lucamar90/ritmo-code/firmware/ritmo_code/ritmo_code.ino

/**
 * Ritmo Code — monitor d'uso per Claude Code, schermo touch LVGL
 * Scheda: Guition JC4832W535 (ESP32-S3, AXS15231B QSPI), 480x320 orizzontale.
 *
 * Dashboard del rate-limit di Claude Code (finestre 5h e 7g, header unified-*),
 * sonda reale per modello (latenza + HTTP), proiezione di esaurimento della
 * finestra 5h e ritmo d'uso orario con filtro di periodo. Token OAuth inserito
 * sullo schermo e salvato cifrato (AES-256-GCM, chiave derivata da un PIN di 4 cifre).
 *
 * Nessun pulsante fisico: navigazione 100% touch (swipe tra le schermate + slideshow).
 * Init di display/touch validato nel bring-up (vedi RIFERIMENTO-HARDWARE-LVGL.md).
 */
#include <Arduino.h>
#include <Arduino_GFX_Library.h>
#include <lvgl.h>
#include <display/lv_display_private.h>   // perf_label / timer del contatore FPS
#include <Wire.h>
#include <WiFi.h>
#include <WebServer.h>
#include <Update.h>
#include <esp_ota_ops.h>
#include <ESPmDNS.h>
#include <Preferences.h>
#include <LittleFS.h>
#include <time.h>
#include <math.h>
#include "config.h"
#include "touch.h"
#include "wifi_manager.h"
#include "api.h"
#include "status.h"
#include "crypto.h"
#include "accounts.h"
#include "extras.h"         // meteo (Open-Meteo) e statistiche del PC per la home
#include "status_page.h"   // pagina di stato servita su /
#include "logo_assets.h"   // Clawd + logotipo ufficiali (generato da tools/gen_logo_assets.py)
struct NoticeText;                 // avviso a schermo intero (prototipi generati da Arduino)
struct AlertRec;                   // voce della cronologia degli avvisi (idem)
struct CdItem;                     // conto alla rovescia (idem)

// ---- Tema "Terminale": font JetBrains Mono (tools/gen_fonts.sh) ----
// 12/14 Regular, 22 Medium, 54 ExtraBold (solo cifre e %). I simboli che JetBrains
// Mono non ha (✻ ↻ ↵ ✎ e lo spinner di Claude Code) arrivano da DejaVu Sans Mono;
// i LV_SYMBOL_* della tastiera LVGL dal fallback Montserrat.
LV_FONT_DECLARE(font_jbm_12)
LV_FONT_DECLARE(font_jbm_14)
LV_FONT_DECLARE(font_jbm_22)
LV_FONT_DECLARE(font_jbm_54)
LV_FONT_DECLARE(font_jbm_96)
LV_FONT_DECLARE(font_jbm_150)
#define F12 (&font_jbm_12)
#define F14 (&font_jbm_14)
#define F22 (&font_jbm_22)
#define F54 (&font_jbm_54)
#define F96 (&font_jbm_96)                  // orologio: solo cifre, due punti e trattino
#define F150 (&font_jbm_150)                // orologio notturno a tutto schermo
#define U_SPARK   "\xE2\x9C\xBB"   // ✻
#define U_REFRESH "\xE2\x86\xBB"   // ↻
#define U_MENU    "\xE2\x89\xA1"   // ≡
#define U_LEFT    "\xE2\x86\x90"   // ←
#define U_RIGHT   "\xE2\x86\x92"   // →
#define U_ENTER   "\xE2\x86\xB5"   // ↵
#define U_UP      "\xE2\x86\x91"   // ↑
#define U_BKSP    "\xE2\x8C\xAB"   // ⌫
#define U_BLOCK   "\xE2\x96\x88"   // █
#define U_CURSOR  "\xE2\x96\x8C"   // ▌
#define U_MIDDOT  "\xC2\xB7"       // ·
#define U_PENCIL  "\xE2\x9C\x8E"   // ✎
#define U_CROSS   "\xE2\x9C\x95"   // ✕

// ---- Palette tema Terminale (stile Claude Code) ----
// Fondo terminale caldo, cornici a 1 px, un solo accento argilla; verde/ambra/rosso
// solo per lo stato.
#define C_BG       0x141413
#define C_SURFACE  0x1B1A18   // tasti e campi di testo
#define C_SURFACE2 0x23221F   // stato "premuto"
#define C_TRACK    0x2C2A27   // blocchi spenti
#define C_GRID     0x2C2A27   // griglie tratteggiate
#define C_BORDER   0x3A3834   // cornici
#define C_TEXT     0xE8E6DF
#define C_MUTED    0x8E8B82
#define C_FAINT    0x5C5A55
#define C_ACCENT   0xD97757   // argilla Claude
#define C_OK       0x9BC08A
#define C_WARN     0xE0B25A
#define C_BAD      0xE06C5A
#define C_BLUE     0x7DB9D6

// ---- Lingua (0 = italiano, 1 = english; Impostazioni -> NVS "lang") ----
// I font JetBrains Mono includono Latin-1: a schermo le lettere accentate ci sono.
static uint8_t g_lang = 0;
#define TRS(pt, en) (g_lang ? (en) : (pt))

// barra a blocchi: due label affiancate (piena + vuota) nello stesso font mono.
// Definita qui in cima: il preprocessore Arduino genera i prototipi prima del codice.
struct Blocks { lv_obj_t *on, *off; int n; };

// ---- Hardware ----
Arduino_Canvas *gfx = nullptr;
static uint16_t *canvas_fb = nullptr;
AXS15231B_Touch touch_dev(TOUCH_SCL, TOUCH_SDA, TOUCH_INT, TOUCH_ADDR, TOUCH_ROTATION);
WiFiManager g_wifi;
Preferences g_prefs;

// ---- Stato dell'applicazione ----
enum State {
  ST_BOOT, ST_PIN, ST_SETUP_PIN, ST_WIFI, ST_TOKEN,
  ST_LOADING, ST_MAIN, ST_SETTINGS, ST_ACCOUNTS, ST_ACCT_NAME, ST_ABOUT, ST_ERROR,
  ST_MODELS, ST_MODEL_EDIT, ST_OTA, ST_NETWORKS
};
static State g_state = ST_BOOT;
static State g_pending = ST_BOOT;
static bool  g_dirty = false;
static void request_state(State s) { g_pending = s; g_dirty = true; }

// ---- Dati ----
static UsageData   g_usage = {};
static ModelStatus g_status = {true, true, true, true, false};

// ---- Modelli sondati (1 per ciclo, a rotazione) ----
// Gli ID si cambiano dal browser (http://<ip>/models) o dal touch (Impostazioni ->
// Modelli) e restano in NVS ("mid0".."mid3"): quando Anthropic rinomina un modello
// basta aggiornare l'ID, senza riflashare. Il nome mostrato resta fisso perche' e'
// legato all'accessorio della mascotte. Nessuna richiesta in piu' alla API: la
// modifica azzera solo il risultato della sonda, che si rifa' al suo turno.
#define NMODELS 4
#define MODEL_ID_MAX 48
struct ModelInfo {
  const char *name; const char *defId; char id[MODEL_ID_MAX]; ProbeResult pr; uint32_t atMs;
  uint16_t lh[7]; uint8_t lhN;          // ultime latenze (mini-linea nella pagina Modelli)
};
static ModelInfo g_models[NMODELS] = {
  {"Haiku",  "claude-haiku-4-5-20251001", "", {0, 0}, 0},
  {"Sonnet", "claude-sonnet-5",           "", {0, 0}, 0},
  {"Opus",   "claude-opus-5-5",           "", {0, 0}, 0},
  {"Fable",  "claude-fable-5-1",          "", {0, 0}, 0},
};
static int g_probeIdx = 0;

// ---- Rete in background (task FreeRTOS sul core 0) ----
// Le chiamate HTTPS (utilizzo, status.claude.com, sonda modello) bloccavano il
// loop per 2-5 s: niente swipe ne' tocchi durante l'aggiornamento. Ora le esegue
// net_task sul core 0 (dove gira gia' lo stack WiFi), mentre LVGL resta libero sul
// core 1. Il task NON tocca mai LVGL, NVS o LittleFS: riempie g_net e alza
// g_netDone; il loop applica i risultati nel proprio thread (net_apply).
struct NetJob {
  // richiesta: scritta dal loop prima di svegliare il task
  char token[200];
  char modelId[MODEL_ID_MAX];
  int  modelIdx;
  uint32_t epoch;          // g_dataEpoch al momento della richiesta
  bool firstLoad;          // true = schermata di caricamento
  // risultato: scritto dal task
  UsageData usage;
  bool usageOk;
  ModelStatus status;
  bool statusOk;
  ProbeResult probe;
  bool probed;
  uint32_t durMs;
};
static NetJob g_net;
static TaskHandle_t g_netTask = nullptr;
static volatile bool g_netBusy = false;   // richiesta in corso (il task possiede g_net)
static volatile bool g_netDone = false;   // risultato pronto da applicare
static bool g_loadPending = false;        // ST_LOADING in attesa che il task sia libero
// Cambia quando token/account cambiano (switch, nuovo token, reset): un risultato
// partito prima appartiene ai dati vecchi e va scartato.
static uint32_t g_dataEpoch = 0;

// ID accettato: 3..47 caratteri a-z 0-9 . - _ (finisce dentro il JSON della sonda)
static bool model_id_valid(const char *v) {
  size_t n = strlen(v);
  if (n < 3 || n >= MODEL_ID_MAX) return false;
  for (size_t i = 0; i < n; i++) {
    char c = v[i];
    if (!((c >= 'a' && c <= 'z') || (c >= '0' && c <= '9') || c == '-' || c == '.' || c == '_'))
      return false;
  }
  return true;
}
static void model_key(int i, char *key, size_t sz) { snprintf(key, sz, "mid%d", i); }
static void models_load() {
  for (int i = 0; i < NMODELS; i++) {
    char key[8]; model_key(i, key, sizeof(key));
    String v = g_prefs.isKey(key) ? g_prefs.getString(key, "") : String();
    strlcpy(g_models[i].id, (v.length() && model_id_valid(v.c_str())) ? v.c_str() : g_models[i].defId,
            MODEL_ID_MAX);
  }
}
// Imposta l'ID del modello i. Vuoto = torna al predefinito. Toglie spazi e
// maiuscole (copia-incolla dalla documentazione). false = ID non valido.
static bool model_set_id(int i, const char *raw) {
  if (i < 0 || i >= NMODELS || !raw) return false;
  char v[MODEL_ID_MAX + 1];
  size_t n = 0;
  for (const char *c = raw; *c; c++) {
    if (*c == ' ' || *c == '\t' || *c == '\r' || *c == '\n') continue;
    if (n >= MODEL_ID_MAX) return false;               // troppo lungo
    v[n++] = (*c >= 'A' && *c <= 'Z') ? (char)(*c + 32) : *c;
  }
  v[n] = 0;
  char key[8]; model_key(i, key, sizeof(key));
  const char *next;
  if (!v[0] || !strcmp(v, g_models[i].defId)) {
    if (g_prefs.isKey(key)) g_prefs.remove(key);
    next = g_models[i].defId;
  } else {
    if (!model_id_valid(v)) return false;
    g_prefs.putString(key, v);
    next = v;
  }
  if (strcmp(next, g_models[i].id) != 0) {
    strlcpy(g_models[i].id, next, MODEL_ID_MAX);
    g_models[i].pr.code = 0; g_models[i].pr.ms = 0; g_models[i].pr.msg[0] = 0;   // "--" fino alla prossima sonda
    g_models[i].atMs = 0;
    g_models[i].lhN = 0;
    Serial.printf("[MODEL] %s -> %s\n", g_models[i].name, g_models[i].id);
  }
  return true;
}


// ---- Token / sicurezza ----
static AccountSlots g_accts;
static EncryptedBlob g_blob;
static bool g_hasToken = false;              // esiste un account salvato in NVS
static bool g_onboarding = false;            // primo setup in corso
static char g_token[200] = {0};              // token decifrato (solo in RAM)
static char g_pendingToken[200] = {0};       // token inserito, in attesa del PIN
// PIN di sessione: resta in RAM dallo sblocco fino al riavvio, perche' cambiare account
// e aggiungerne uno richiedono di decifrare/cifrare ALTRI slot senza richiedere il PIN.
// Compromesso accettato: non indebolisce il modello — il token vive GIA' decifrato in
// g_token, quindi chi riesce a leggere la RAM ha gia' cio' che conta. Resta valido
// che: niente di tutto questo finisce in NVS, e factory_reset() azzera questo buffer.
static char g_sessionPin[PIN_LEN + 1] = {0};
static int  g_tokenTargetSlot = 0;
static char g_pendingLabel[ACCT_LBL_MAX] = {0};
static char g_pinEntry[PIN_LEN + 1] = {0};   // cifre in digitazione
static bool g_pinForWipe = false;            // schermata PIN aperta per confermare "cancella tutto"
static char g_pinFirst[PIN_LEN + 1] = {0};   // 1° inserimento nel setup del PIN
static bool g_pinConfirming = false;         // setup: conferma (2° inserimento)
static int  g_pinAttempts = 0;               // tentativi errati (persistito)
static uint32_t g_lockoutUntil = 0;          // millis fino al prossimo tentativo consentito
static bool g_timeInit = false;

// ---- Refresh in background ----
static bool g_wantRefresh = false;        // il pulsante di refresh ha chiesto un aggiornamento
static bool g_refreshing = false;         // richiesta in corso
static bool g_lastFetchOk = true;         // l'ultimo fetch e' andato a buon fine?
static char g_lastErr[64] = "";           // errore dell'ultimo fetch fallito (pannello web, /api/status)
static uint32_t g_lastErrAt = 0;          // epoch dell'errore
static int g_failN = 0;                   // fetch falliti di fila
static uint32_t g_lastOkMs = 0;           // millis dell'ultimo successo (per "aggiornato Xs fa")
static lv_obj_t *g_hdrStatus = nullptr;   // testo di stato nell'intestazione del dashboard

// ---- Fuso orario ----
// TZ_ROME usa la regola POSIX CET/CEST: l'ora legale cambia da sola (ultima
// domenica di marzo / ottobre). Gli altri valori sono offset GMT fissi.
#define TZ_ROME     99
#define TZ_ROME_RULE "CET-1CEST,M3.5.0,M10.5.0/3"

// ---- Luminosita' ----
static const uint8_t BRI_LEVELS[3] = {60, 160, 255};
static int g_briIdx = 1;
// luminosita' automatica: piena di giorno, bassa la sera (NVS "autobri")
// 0 spento, 1 col sole (tramonto-alba dal meteo, altrimenti 20-07), 2 20:00-07:00, 3 21:00-07:00
static int g_autoBri = 0;
// promemoria pausa (NVS "brk"): dopo N minuti di PC in uso senza staccare (dal PC Monitor)
static int g_brkIdx = 0;
static const uint8_t BRK_MIN[4] = {0, 45, 60, 90};
// avviso settimana (NVS "wkal"): sopra la soglia, se a questo ritmo la quota finisce almeno
// 12 ore prima del reset. Una volta per settimana ("wkald" = reset della settimana avvisata)
static int g_wkAlIdx = 2;
static const uint8_t WK_AL_THR[4] = {0, 70, 85, 95};
static uint32_t g_wkAlDone = 0;
// tasti della tendina (NVS "shbtn"): un bit per tasto, al massimo quattro
enum { SHB_PAUSE = 0, SHB_TIMER, SHB_LIGHT, SHB_SOUND, SHB_REFRESH, SHB_CAL, SHB_WX, SHB_MEDIA, SHB_CD, SHB_N };
static uint16_t g_shBtn = 0x0F;
// Claude oggi (NVS "ccd" giorno, "ccn" richieste finite, "cct" secondi di lavoro, "ccx" la piu' lunga)
static long g_ccDay = 0;
static int  g_ccN = 0;
static uint32_t g_ccT = 0, g_ccX = 0;
// ---- Media in riproduzione sul PC (PC Monitor 1.8): pagina a tutto schermo con copertina 160x160 ----
#define MC_N 160
static bool g_mediaAuto = true;                  // la pagina si apre da sola quando parte la riproduzione (NVS "mauto")
static bool g_mediaFast = false;                 // pagina aperta: il PC si legge ogni secondo
static uint8_t *g_mcImg = nullptr, *g_mcTmp = nullptr;   // copertina (PSRAM): mostrata / in arrivo dal task extra
static lv_image_dsc_t g_mcDsc;
static bool g_mcHave = false;
static uint32_t g_mcId = 0, g_mcWant = 0, g_mcGot = 0, g_mcPosAtMs = 0;
static volatile bool g_mcReq = false, g_mcDone = false, g_mcOk = false, g_mcActReq = false;
static char g_mcHost[48], g_mcAct[10];
static volatile bool g_ssReq = false;           // pagina sessioni: apri la sessione g_ssKey sul PC
static char g_ssHost[48], g_ssKey[10];
static bool g_ssTab = true;                     // cerca anche la scheda giusta in Warp (NVS "sstab")
static char g_ssAskK[10] = "";                  // ultima sessione toccata (esito sotto il riquadro)
// sulla pagina sessioni gli avvisi di Claude non aprono lo schermo intero: lampeggia il riquadro
// della sessione che ha appena finito o che aspetta te (fino al tocco o per 60 s)
static char g_ssBlinkK[6][10];
static uint32_t g_ssBlinkMs[6];
static char g_ssPrevK[6][10];
static int g_ssPrevS[6];
static uint32_t g_ssAskMs = 0;
static int g_mcSec = 0;
// ---- Conto alla rovescia verso una data (NVS "cd0".."cd2": "epoch|titolo"), dal dispositivo o dal browser ----
struct CdItem { uint32_t at; char title[44]; };
#define CD_MAX 3
static CdItem g_cd[CD_MAX];
static int g_cdN = 0, g_cdSel = 0;
static bool g_cdAlerted[CD_MAX];
static void cd_load();
static void cd_view_refresh();                  // ridisegna la pagina se e' aperta
static int cd_home_idx(time_t now);             // il conto da mostrare in home, -1 nessuno
static void cd_view_build();
static void cd_parts(const CdItem &c, time_t now, char *big, char *unit, char *sub, size_t n);
static bool g_cdOpen = false;                   // conto alla rovescia o editor aperti

static uint32_t g_lastPollMs = 0;         // millis dell'ultimo poll (per la barra di refresh)
static int g_pollSec = DEFAULT_POLL_SEC;  // intervallo di aggiornamento (config, NVS)
static int g_tzOffset = TZ_ROME;          // fuso: TZ_ROME (ora legale auto) o offset GMT fisso, NVS
static int g_slideSec = 0;                // slideshow: 0=off, 5/10/15/30s (config, NVS)
static int g_heatSrc = 0;                 // pagina ritmo: 0 claude, 1 pomodoro (NVS "heats")
static int g_heatMode = 3;                // 0=oggi 1=7g 2=30g 3=tutto (config, NVS)
static bool g_resetAlert = true;          // avviso quando una finestra oltre l'80% si libera (NVS "rstal")
static bool g_pcSound = true;             // suoni e notifiche sul PC per gli avvisi (NVS "pcsnd")
static int  g_ccCloseIdx = 2;             // chiude da solo l'avviso di Claude: 5 s, 10 s, 30 s, mai (NVS "ccclose")
static const uint8_t CC_CLOSE_S[4] = {5, 10, 30, 0};
static int  g_ccAlert = 2;                // avvisi di Claude Code: 0 spento, 1 sempre, 2/3 fine lavoro oltre 1/5 min (NVS "ccal")

// ---- Diagnostica prestazioni (Impostazioni -> Contatore FPS, NVS "perf") ----
// A schermo: overlay LVGL "FPS, CPU / ms (render | flush)". Sul seriale ogni 2s:
// fps, tempo di rotazione del frame, tempo di invio QSPI, loop piu' lento e
// memoria libera. Il tempo delle chiamate di rete viene stampato a ogni refresh.
// Nota: con il render FULL anche l'overlay stesso forza un ridisegno ogni ~300ms.
static bool g_perfOn = false;
struct PerfStats {
  uint32_t frames;
  uint64_t rotUs, copyUs, waitUs, txUs;
  uint32_t rotMaxUs, copyMaxUs, waitMaxUs, txMaxUs;
  uint32_t txFrames;       // frame inviati dal task del display (core 0)
  uint32_t loopMaxMs;
};
static PerfStats g_perf = {};
static uint32_t g_lastTouchMs = 0;        // ultimo tocco (mette in pausa lo slideshow)
// Notte / attenuazione (NVS "night", "nightp", "dim"). Valgono solo sul dashboard.
static const uint8_t NIGHT_FROM[4] = {0, 22, 23, 0};     // indice 0 = spento
static int  g_nightIdx = 0;                    // 0 spento, 1 22-07, 2 23-07, 3 00-07
static bool g_nightPause = true;               // di notte niente richieste ad Anthropic
static int  g_dimIdx = 0;                      // 0 spento, poi DIM_MIN minuti senza tocchi
static const uint8_t DIM_MIN[4] = {0, 1, 5, 10};
#define NIGHT_WAKE_MS 30000UL                  // di notte un tocco accende per 30 s
#define DIM_LEVEL 12                           // duty del backlight attenuato
static bool g_userPause = false;               // richieste messe in pausa dal tasto in testata (NVS "pause")
static uint32_t g_pauseUntil = 0;              // epoch di ripresa automatica, 0 = senza limite (NVS "pauseu")
static int  g_clockIdx = 0;                    // torna alla home dopo: 0 spento, poi CLOCK_MIN minuti (NVS "clock")
static const uint8_t CLOCK_MIN[4] = {0, 2, 5, 10};
// ---- Home: meteo e PC (task "extra" sul core 0, mai richieste ad Anthropic) ----
static float g_wxLat = DEFAULT_WX_LAT, g_wxLon = DEFAULT_WX_LON;   // NVS "wxlat", "wxlon"
static char  g_wxCity[32] = DEFAULT_WX_CITY;                        // NVS "wxcity"
static char  g_pcHost[48] = DEFAULT_PC_HOST;                        // NVS "pchost" (Ritmo Code PC Monitor, ip:porta)
static float g_kwhPrice = 0.30f;                                    // euro per kWh (NVS "kwh", /home)
static WeatherData g_wx = {};
static PcStats g_pc = {};
static uint32_t g_wxAtMs = 0, g_wxTryMs = 0, g_pcAtMs = 0, g_pcTryMs = 0;
static volatile bool g_wxReq = false, g_wxDone = false, g_pcReq = false, g_pcDone = false;
static WeatherData g_wxRes = {};
static PcStats g_pcRes = {};
static char g_pcReqHost[48] = {0};
// avviso da mandare al PC (task "extra"): l'ultimo vince
struct PcNotify { char host[48], ev[8], title[64], msg[96]; };
static PcNotify g_pcNtf = {};
static volatile bool g_pcNtfReq = false;
static SemaphoreHandle_t g_httpsLock = nullptr;
#define PC_HIST 240                                 // grafici: un punto per lettura (1 s = 4 min, 5 s = 20 min)
static int g_pcIntIdx = 0;                          // intervallo di lettura del PC (NVS "pcint")
static const uint16_t PC_INT_S[4] = {1, 3, 5, 60};
static uint32_t g_pcHistAtMs = 0;
// il PC e' considerato spento se non risponde da 3 letture (almeno 20 s)
static uint32_t pc_stale_ms() { uint32_t m = 3000UL * PC_INT_S[g_pcIntIdx]; return m < 20000UL ? 20000UL : m; }
static uint32_t pc_int_ms() { return g_mediaFast ? 1000UL : PC_INT_S[g_pcIntIdx] * 1000UL; }
static void pc_poll_in(uint32_t ms) { g_pcTryMs = millis() + ms + 50 - pc_int_ms(); }   // prossima lettura tra ms
static uint8_t g_pcHist[3][PC_HIST];               // cpu, gpu, ram in %
static int g_pcHistN = 0;
static lv_point_precise_t g_pcSparkPts[3][PC_HIST];   // una sola connessione TLS alla volta (RAM interna)
static uint8_t g_screenMode = 0;               // 0 normale, 1 attenuato, 2 spento, 3 orologio notturno
static bool g_nightClock = true;               // di notte: orologio tenue invece dello schermo spento (NVS "nightclk")
static int  g_nightBri = 0;                    // luminosita' dell'orologio notturno: 0 tenue, 1 molto tenue (NVS "nightbri")
static const uint8_t NIGHT_BRI[2] = {18, 6};
static bool g_touchSwallow = false;            // il tocco che risveglia non preme nulla
static uint32_t g_lastSlideMs = 0;

// ---- Storico (ring buffer; persistito in LittleFS) ----
#define HIST_MAX 160
struct Sample { uint32_t t; uint8_t h5; uint8_t d7; };   // t = epoch (0 = orologio non sincronizzato)
static Sample g_hist[HIST_MAX];
static int g_histN = 0;
static int g_histHead = 0;
static float g_hourBurn[24] = {0};   // consumo per ora del giorno (da sempre)
static float g_lastH5 = -1.0f;       // ultimo utilizzo 5h (delta dell'heatmap)

// ---- Picco di ogni settimana (per account, /weeks<slot>.bin) ----
#define NWEEKS 12
struct WeekRec { uint32_t reset; uint8_t peak; };    // reset = epoch di fine settimana
static WeekRec g_weeks[NWEEKS];
static int g_weekN = 0;

// ---- Heatmap per giorno (per il filtro oggi/7g/30g) ----
#define NDAYS 31
struct DayHeat { uint32_t day; float burn[24]; };   // day = giorni locali dall'epoch
static DayHeat g_days[NDAYS];
static int g_dayN = 0;

// ---- Mascotte Clawd ufficiali (pagina modelli; umore in base allo stato) ----
// mood: 0=mai sondato, 1=ok, 2=limitato(429), 3=errore/incidente, 4=n/d(404)
struct Mascot { lv_obj_t *cont, *img, *lid[2], *drop; int baseY, mood; };
static Mascot g_masc[NMODELS];
static int g_mascN = 0;
static lv_point_precise_t g_mXPts[NMODELS][4][2];   // occhi a X (mood 3)

// ---- Puntatori UI del dashboard (azzerati a ogni build di ST_MAIN) ----
#define NTILES 8
// Pagine: l'ordine si sceglie in Impostazioni > schermo > ordine pagine (NVS "porder"); la home resta
// la prima. g_pageOrder[tile] = pagina mostrata in quella posizione.
enum { PG_HOME = 0, PG_ORA, PG_SESS, PG_MODELS, PG_5H, PG_RITMO, PG_WEEKS, PG_PC };
static uint8_t g_pageOrder[NTILES] = {PG_HOME, PG_ORA, PG_SESS, PG_MODELS, PG_5H, PG_RITMO, PG_WEEKS, PG_PC};
static int g_curTile = 0;
static int cur_page() { return g_pageOrder[g_curTile < NTILES ? g_curTile : 0]; }
static int tile_of(int pg) { for (int i = 0; i < NTILES; i++) if (g_pageOrder[i] == pg) return i; return 0; }
static const char *page_name(int pg);
#define NBLK 19                       // blocchi della barra di utilizzo
struct DashUI {
  lv_obj_t *tv, *tile[NTILES], *tab[NTILES];
  lv_obj_t *hdrPath, *hdrAcct, *refBar, *pauseBtn, *pauseBar[2], *pausePlay;
  lv_obj_t *hdrSpark, *hmClLegend;                // ✻ che gira e "claude · al lavoro" quando Claude lavora
  // ora
  lv_obj_t *agPct5, *agCd5, *agAt5, *agPct7, *agCd7, *agAt7;
  lv_obj_t *agFc5;                                // previsione della 5h sotto il conto alla rovescia
  lv_obj_t *ssBox[6], *ssLeg[6], *ssSt[6], *ssAge[6], *ssTi[6], *ssFt[6];   // pagina sessioni
  Blocks blk5, blk7;
  lv_obj_t *agWord, *agCursor, *agPace, *agPaceMark;
  // modelli
  lv_obj_t *mDot[NMODELS], *mName[NMODELS], *mSpark[NMODELS], *mLat[NMODELS], *mStat[NMODELS];
  lv_obj_t *mSum, *mInc;
  // finestra 5h
  lv_obj_t *trHist, *trProj, *trDot, *trCap, *trT0, *trT1;
  // ritmo
  lv_obj_t *heat[24], *heatBtn[4], *heatTab[2], *heatCap;
  // settimane
  lv_obj_t *wkBar[8], *wkVal[8], *wkDate[8], *wkCap;
  // home
  lv_obj_t *hmTime, *hmDate, *hmWxIcon, *hmTemp, *hmDesc, *hmRain, *hmSun;
  lv_obj_t *hmPct[2], *hmInfo[2], *hmRight[2];
  Blocks hmBlk[2];
  lv_obj_t *hmPcRow, *hmPcOff, *hmPcVal[4], *hmPcLegend;
  lv_obj_t *hmPauseRow;                           // "richieste" + "in pausa" (in giallo): due colori, due etichette
  lv_obj_t *hmCdLegend, *hmCdBig, *hmCdUnit, *hmCdSec;   // conto alla rovescia in home (a destra del riquadro claude)
  bool hmCdOn;
  // pc
  lv_obj_t *pcLeg[4], *pcMain[4], *pcSub[3], *pcSpark[3], *pcSys, *pcDisks;
  int hmWxCode;
};
static DashUI g_ui;
static lv_obj_t *g_pinDots = nullptr, *g_pinMsg = nullptr;

// punti delle linee del grafico di tendenza (devono restare validi)
static lv_point_precise_t g_trPts[HIST_MAX];
static lv_point_precise_t g_trProjPts[2];

// ---- Forward declarations ----
static void render_state();
static void refresh_ui_values();
static void dash_tick();
static void set_hdr_status();
static void apply_tz();
static void ui_pin();
static void ui_wifi();
static void ui_token();
static void ui_loading(const char *sub);
static void ui_main();
static void ui_settings();
static void ui_accounts();
static void ui_account_name();
static void ui_models();
static void perf_apply();
static void ui_model_edit();
static void ui_ota();
static void ui_networks();
static void ui_message(const char *title, const char *sub, uint32_t color);
static void nav_cb(lv_event_t *e);
static void start_data_web();
static void trend_redraw();
static void heat_redraw();
static void weeks_redraw();
static void home_redraw();
static void home_tick();
static void pc_redraw();
static void pause_menu_close();
static void show_moment(int win, int thr);
static void moment_tick();
static void moment_close();
static void cc_event(long id, const char *ev, const char *proj, int dur, int age);
static int g_setGroup = 0;
// calendario: link iCal (NVS "ical", segreto: lo legge solo il PC collegato) e prossimi eventi dal PC Monitor
static char g_ical[256] = "";
struct CalEv { uint32_t s, e; char title[64]; };
static CalEv g_cal[3];
static int g_calN = 0;
static int g_calAlIdx = 1;                   // avviso calendario: 0 spento, 1/2/3 = 5/10/15 min prima (NVS "calal")
static const uint8_t CAL_AL_MIN[4] = {0, 5, 10, 15};
static uint32_t g_calAlerted = 0;            // inizio dell'ultimo evento gia' avvisato
static CalEv g_calNotice;                    // evento dell'avviso a schermo
#define CAL_ALL_MAX 120
static CalItem *g_calTmp = nullptr;            // download del task extra, copiato nel loop
static int g_tmMenuMode = 0;                  // menu del timer: 0 tutto, 1 solo pomodoro, 2 solo timer
static bool g_ccFocusDefer = false;          // avvisi di Claude durante il focus: rimandati alla pausa (NVS "ccfocus")
static bool g_ccDeferred = false;            // un avviso di Claude aspetta la fine del focus
static bool tm_action(int opt);               // comandi del timer (menu del dispositivo e PC)
static uint32_t tm_left_s();
// pannello a tendina: il touch riconosce il gesto (giu' dalla testata / su per chiudere), il loop apre
static volatile int g_shadeReq = 0;               // 1 apri, 2 chiudi
static lv_obj_t *g_shade = nullptr;
// Aggiornamento del firmware dall'ultima release di GitHub: controllo (task extra) e installazione
// (task di rete: scrivere la flash da uno stack in PSRAM non si puo')
enum { UPD_IDLE = 0, UPD_CHECKING, UPD_AVAILABLE, UPD_UPTODATE, UPD_ERROR, UPD_INSTALLING, UPD_FAILED, UPD_REBOOT };
static volatile int g_updState = UPD_IDLE;
static volatile bool g_updCheckReq = false, g_updInstallReq = false, g_updRunning = false, g_updDone = false;
static volatile int g_updPct = 0;
static char g_updTag[16] = "", g_updUrl[200] = "";
static String g_updErr;
static uint32_t g_updCheckedMs = 0;
static uint32_t g_updCheckStartMs = 0;        // "controllo..." resta a schermo almeno 1,5 s
static void upd_progress(int pct) { g_updPct = pct; }
// "v3.9.3" piu' recente di FW_VERSION? (confronto numero per numero)
static bool ver_newer(const char *tag) {
  int a[3] = {0, 0, 0}, b[3] = {0, 0, 0};
  const char *t = tag; while (*t && !isdigit((unsigned char)*t)) t++;
  sscanf(t, "%d.%d.%d", &a[0], &a[1], &a[2]);
  sscanf(FW_VERSION, "%d.%d.%d", &b[0], &b[1], &b[2]);
  for (int i = 0; i < 3; i++) if (a[i] != b[i]) return a[i] > b[i];
  return false;
}                   // gruppo di impostazioni aperto (0 = pagina principale)
static char g_ccEv[8], g_ccProj[28];
static int  g_ccBusyN = 0;                      // sessioni di Claude Code al lavoro (PC Monitor)
static void cc_busy_ui();            // ultimo evento di Claude Code da mostrare
static void tm_menu_open(lv_event_t *e);
static void tm_label(char *out, size_t sz);
static uint32_t tm_color();
enum { TM_OFF = 0, TM_TIMER, TM_FOCUS, TM_BREAK };
static int  g_tmMode = TM_OFF;                // timer/pomodoro in corso
static int  g_pomoToday = 0;                  // pomodori completati oggi (NVS "pomn", giorno in "pomday")
static long g_pomoDay = 0;
static int  pomo_today();
static uint32_t g_tmEndMs = 0, g_tmLenS = 0;
static int  g_pomoN = 0;                      // pomodori completati nel ciclo in corso
// pomodoro: tre impostazioni pronte (focus / pausa / pausa lunga dopo il quarto, in minuti)
struct PomoPreset { uint8_t focus, brk, lng; };
static const PomoPreset POMO_PRESETS[3] = {{25, 5, 15}, {50, 10, 20}, {15, 3, 10}};
static int g_pomoPre = 0;                     // impostazione del ciclo in corso
#define POMO_FOCUS_S (POMO_PRESETS[g_pomoPre].focus * 60)
#define POMO_SHORT_S (POMO_PRESETS[g_pomoPre].brk * 60)
#define POMO_LONG_S  (POMO_PRESETS[g_pomoPre].lng * 60)
#define POMO_CYCLE   4

// ============================================================
// Pipeline di display/touch (validata nel bring-up)
// ============================================================
// Render PARZIALE: LVGL consegna solo le zone cambiate (a strisce, dal buffer
// piccolo in RAM interna). Ogni zona viene ruotata di 270 gradi nel framebuffer
// del Canvas (320x480, PSRAM) e, all'ultima zona del ciclo, il frame intero parte
// verso il pannello: l'AXS15231B di questa scheda non gestisce bene le finestre
// parziali, quindi l'invio resta a schermo intero.
// Mappatura invariata rispetto al bring-up: fb[(479 - x) * 320 + y] = pixel(x, y).
// Il ciclo esterno su x scrive il framebuffer in blocchi contigui (una riga del
// pannello per x): con la PSRAM dietro la cache e' ~decine di volte piu' veloce
// della vecchia copia a salti.
// ---- Invio del frame in parallelo (task "disp" sul core 0) ----
// L'invio QSPI del frame intero costa ~40 ms e prima bloccava LVGL. Ora:
//  - core 1 (LVGL) ruota le zone cambiate in canvas_fb, che resta l'immagine
//    completa e aggiornata;
//  - a fine frame aspetta che l'invio precedente sia finito, copia in tx_fb SOLO
//    il rettangolo cambiato in questo frame e sveglia il task;
//  - core 0 spedisce tx_fb al pannello mentre LVGL disegna gia' il frame dopo.
// tx_fb riceve ogni frame (nessuno viene saltato), quindi resta identico a
// canvas_fb dopo ogni copia: niente tearing, niente righe a meta' fra due frame.
static Arduino_GFX *g_panel = nullptr;        // driver AXS15231B (sotto al Canvas)
static uint16_t *tx_fb = nullptr;             // copia stabile del frame da inviare (PSRAM)
static SemaphoreHandle_t g_txIdle = nullptr;  // libero = nessun invio in corso
static TaskHandle_t g_txTask = nullptr;
static uint32_t g_frameRotUs = 0;
static int g_dirtyR0 = 480, g_dirtyR1 = -1, g_dirtyC0 = 320, g_dirtyC1 = -1;   // coordinate pannello

static void disp_tx_task(void *) {
  for (;;) {
    ulTaskNotifyTake(pdTRUE, portMAX_DELAY);
    uint32_t t0 = micros();
    g_panel->draw16bitRGBBitmap(0, 0, tx_fb, 320, 480);
    uint32_t tx = micros() - t0;
    g_perf.txFrames++;
    g_perf.txUs += tx; if (tx > g_perf.txMaxUs) g_perf.txMaxUs = tx;
    xSemaphoreGive(g_txIdle);
    // L'invio QSPI e' a polling e non cede mai la CPU: senza questa pausa, con lo
    // spinner che anima a ~27 fps e il TLS del task di rete sullo stesso core,
    // l'idle del core 0 non girava piu' e il task watchdog riavviava la scheda.
    vTaskDelay(1);
  }
}

static void disp_flush_cb(lv_display_t *disp, const lv_area_t *area, uint8_t *px_map) {
  uint32_t t0 = micros();
  const uint16_t *src = (const uint16_t *)px_map;
  int w = area->x2 - area->x1 + 1;
  int h = area->y2 - area->y1 + 1;
  for (int i = 0; i < w; i++) {
    uint16_t *dst = canvas_fb + (479 - (area->x1 + i)) * 320 + area->y1;
    const uint16_t *s = src + i;
    for (int j = 0; j < h; j++, s += w) dst[j] = *s;
  }
  // rettangolo cambiato, in coordinate del pannello (riga = 479 - x, colonna = y)
  if (479 - area->x2 < g_dirtyR0) g_dirtyR0 = 479 - area->x2;
  if (479 - area->x1 > g_dirtyR1) g_dirtyR1 = 479 - area->x1;
  if (area->y1 < g_dirtyC0) g_dirtyC0 = area->y1;
  if (area->y2 > g_dirtyC1) g_dirtyC1 = area->y2;
  g_frameRotUs += micros() - t0;

  if (lv_display_flush_is_last(disp)) {
    uint32_t t1 = micros();
    xSemaphoreTake(g_txIdle, portMAX_DELAY);          // invio precedente finito
    uint32_t t2 = micros();
    if (g_dirtyR1 >= g_dirtyR0 && g_dirtyC1 >= g_dirtyC0) {
      size_t n = (size_t)(g_dirtyC1 - g_dirtyC0 + 1) * sizeof(uint16_t);
      for (int r = g_dirtyR0; r <= g_dirtyR1; r++)
        memcpy(tx_fb + r * 320 + g_dirtyC0, canvas_fb + r * 320 + g_dirtyC0, n);
    }
    uint32_t t3 = micros();
    g_dirtyR0 = 480; g_dirtyR1 = -1; g_dirtyC0 = 320; g_dirtyC1 = -1;
    xTaskNotifyGive(g_txTask);                        // parte l'invio sul core 0

    uint32_t wait = t2 - t1, copy = t3 - t2;
    g_perf.frames++;
    g_perf.rotUs  += g_frameRotUs; if (g_frameRotUs > g_perf.rotMaxUs) g_perf.rotMaxUs = g_frameRotUs;
    g_perf.waitUs += wait;         if (wait > g_perf.waitMaxUs)        g_perf.waitMaxUs = wait;
    g_perf.copyUs += copy;         if (copy > g_perf.copyMaxUs)        g_perf.copyMaxUs = copy;
    g_frameRotUs = 0;
  }
  lv_disp_flush_ready(disp);
}
static void screen_apply();
static bool g_touchDown = false, g_gestDone = false;
static int16_t g_gestX = 0, g_gestY = 0;
static void touch_gesture_reset() { g_touchDown = false; }
static void touch_read_cb(lv_indev_t *indev, lv_indev_data_t *data) {
  uint16_t x, y;
  if (touch_dev.touched()) {
    touch_dev.readData(&x, &y);
    g_lastTouchMs = millis();          // mette in pausa lo slideshow durante l'interazione
    if (g_screenMode != 0) {           // schermo spento/attenuato: il tocco serve solo a risvegliare
      g_touchSwallow = true;
      g_screenMode = 0;
      screen_apply();
    }
    if (g_touchSwallow) { data->state = LV_INDEV_STATE_RELEASED; return; }
    // pannello a tendina: giu' partendo dalla testata apre, su chiude (piu' verticale che orizzontale)
    if (!g_touchDown) { g_touchDown = true; g_gestDone = false; g_gestX = x; g_gestY = y; }
    int16_t sx = g_gestX, sy = g_gestY; bool &done = g_gestDone;
    int dy = (int)y - sy, dx = abs((int)x - sx);
    if (!done && g_state == ST_MAIN) {
      if (!g_shade && sy < 40 && dy > 35 && dy > 2 * dx) { g_shadeReq = 1; done = true; }
      else if (g_shade && dy < -35 && -dy > 2 * dx)    { g_shadeReq = 2; done = true; }
      if (done) { g_touchSwallow = true; data->state = LV_INDEV_STATE_RELEASED; return; }
    }
    data->point.x = x; data->point.y = y;
    data->state = LV_INDEV_STATE_PRESSED;
  } else {
    g_touchSwallow = false;
    data->state = LV_INDEV_STATE_RELEASED;
    touch_gesture_reset();
  }
}

// ============================================================
// Helper di UI
// ============================================================
// Aggiornano una label solo se testo/colore cambiano davvero: ogni modifica
// invalida l'area e, con il pannello che vuole il frame intero, costa ~40 ms di invio.
static void label_set(lv_obj_t *l, const char *txt) {
  if (!l) return;
  const char *cur = lv_label_get_text(l);
  if (cur && strcmp(cur, txt) == 0) return;
  lv_label_set_text(l, txt);
}
static void label_color(lv_obj_t *l, uint32_t col) {
  if (!l) return;
  lv_color_t c = lv_color_hex(col);
  if (lv_color_eq(lv_obj_get_style_text_color(l, LV_PART_MAIN), c)) return;
  lv_obj_set_style_text_color(l, c, 0);
}
static lv_obj_t *mklabel(lv_obj_t *p, const char *txt, const lv_font_t *font, uint32_t color) {
  lv_obj_t *l = lv_label_create(p);
  lv_label_set_text(l, txt);
  lv_obj_set_style_text_font(l, font, 0);
  lv_obj_set_style_text_color(l, lv_color_hex(color), 0);
  return l;
}
static void no_box(lv_obj_t *o) {
  lv_obj_set_style_bg_opa(o, 0, 0);
  lv_obj_set_style_border_width(o, 0, 0);
  lv_obj_set_style_pad_all(o, 0, 0);
  lv_obj_clear_flag(o, LV_OBJ_FLAG_SCROLLABLE);
}
// colore per soglia, a gradini come in un terminale: <50 ok, <80 argilla, poi rosso
static uint32_t level_hex(float p) {
  if (p >= 80.0f) return C_BAD;
  if (p >= 50.0f) return C_ACCENT;
  return C_OK;
}
static lv_color_t grad_color(float p) { return lv_color_hex(level_hex(p)); }

// ---------- primitive del tema Terminale ----------
// Oggetti senza stili del tema LVGL: niente ombre, padding o sfondi da calcolare.
static lv_obj_t *plain_obj(lv_obj_t *p) {
  lv_obj_t *o = lv_obj_create(p);
  lv_obj_remove_style_all(o);
  lv_obj_clear_flag(o, LV_OBJ_FLAG_SCROLLABLE);
  lv_obj_clear_flag(o, LV_OBJ_FLAG_CLICKABLE);
  return o;
}
static lv_obj_t *hline(lv_obj_t *p, int x, int y, int w, uint32_t col) {
  lv_obj_t *o = plain_obj(p);
  lv_obj_set_pos(o, x, y); lv_obj_set_size(o, w, 1);
  lv_obj_set_style_bg_color(o, lv_color_hex(col), 0);
  lv_obj_set_style_bg_opa(o, LV_OPA_COVER, 0);
  return o;
}
// linea orizzontale tratteggiata: i punti devono restare validi (static)
static lv_point_precise_t PTS_W404[2] = {{0, 0}, {404, 0}};
static lv_point_precise_t PTS_W440[2] = {{0, 0}, {440, 0}};
static lv_obj_t *dline(lv_obj_t *p, int x, int y, lv_point_precise_t *pts) {
  lv_obj_t *l = lv_line_create(p);
  lv_obj_set_pos(l, x, y);
  lv_line_set_points(l, pts, 2);
  lv_obj_set_style_line_width(l, 1, 0);
  lv_obj_set_style_line_color(l, lv_color_hex(C_GRID), 0);
  lv_obj_set_style_line_dash_width(l, 3, 0);
  lv_obj_set_style_line_dash_gap(l, 3, 0);
  lv_obj_clear_flag(l, LV_OBJ_FLAG_CLICKABLE);
  return l;
}
// riquadro a filo sottile con il titolo inciso nella cornice
static lv_obj_t *tbox(lv_obj_t *p, int x, int y, int w, int h, const char *legend,
                      uint32_t col = C_BORDER, lv_obj_t **legendOut = nullptr) {
  lv_obj_t *b = plain_obj(p);
  lv_obj_set_pos(b, x, y); lv_obj_set_size(b, w, h);
  lv_obj_set_style_border_width(b, 1, 0);
  lv_obj_set_style_border_color(b, lv_color_hex(col), 0);
  lv_obj_set_style_radius(b, 4, 0);
  if (legend) {
    // Il titolo e' fratello del riquadro, non figlio: da figlio LVGL tagliava la parte
    // che sporge sopra il bordo. Sfondo pieno per "interrompere" la cornice.
    lv_obj_t *l = mklabel(p, legend, F12, C_MUTED);
    lv_obj_set_style_bg_color(l, lv_color_hex(C_BG), 0);
    lv_obj_set_style_bg_opa(l, LV_OPA_COVER, 0);
    lv_obj_set_style_pad_hor(l, 5, 0);
    lv_obj_set_pos(l, x + 8, y - 8);            // testo a x+13, allineato al rientro dei contenuti
    if (legendOut) *legendOut = l;
  }
  return b;
}
// pulsante: cornice 1 px, testo centrato, sfondo solo quando premuto
static lv_obj_t *tbtn(lv_obj_t *p, int x, int y, int w, int h, const char *txt, const lv_font_t *f,
                      uint32_t fg, uint32_t border, lv_event_cb_t cb, void *ud) {
  lv_obj_t *b = plain_obj(p);
  lv_obj_set_pos(b, x, y); lv_obj_set_size(b, w, h);
  lv_obj_set_style_border_width(b, 1, 0);
  lv_obj_set_style_border_color(b, lv_color_hex(border), 0);
  lv_obj_set_style_radius(b, 4, 0);
  lv_obj_set_style_bg_color(b, lv_color_hex(C_SURFACE2), LV_STATE_PRESSED);
  lv_obj_set_style_bg_opa(b, LV_OPA_COVER, LV_STATE_PRESSED);
  lv_obj_add_flag(b, LV_OBJ_FLAG_CLICKABLE);
  lv_obj_set_ext_click_area(b, 6);
  lv_obj_center(mklabel(b, txt, f, fg));
  if (cb) lv_obj_add_event_cb(b, cb, LV_EVENT_CLICKED, ud);
  return b;
}
// contenitore riga (flex) per comporre testi di colori diversi
static lv_obj_t *trow(lv_obj_t *p, int x, int y) {
  lv_obj_t *r = plain_obj(p);
  lv_obj_set_pos(r, x, y);
  lv_obj_set_size(r, LV_SIZE_CONTENT, LV_SIZE_CONTENT);
  lv_obj_set_flex_flow(r, LV_FLEX_FLOW_ROW);
  lv_obj_set_flex_align(r, LV_FLEX_ALIGN_START, LV_FLEX_ALIGN_END, LV_FLEX_ALIGN_END);
  return r;
}
static Blocks blocks_create(lv_obj_t *p, int x, int y, int n, const lv_font_t *f) {
  lv_obj_t *r = trow(p, x, y);
  Blocks b = { mklabel(r, "", f, C_ACCENT), mklabel(r, "", f, C_TRACK), n };
  return b;
}
static void blocks_set(Blocks &b, float pct, uint32_t col) {
  if (!b.on) return;
  int f = (int)(pct / 100.0f * b.n + 0.5f);
  if (pct > 0.5f && f == 0) f = 1;
  if (f < 0) f = 0; if (f > b.n) f = b.n;
  char on[3 * NBLK + 1] = "", off[3 * NBLK + 1] = "";
  for (int i = 0; i < f; i++) strcat(on, U_BLOCK);
  for (int i = f; i < b.n; i++) strcat(off, U_BLOCK);
  label_set(b.on, on);
  label_set(b.off, off);
  label_color(b.on, col);
}
// intestazione delle schermate secondarie: ✻ titolo, [← indietro], filo
static void nav_cb(lv_event_t *e);
static void thead(lv_obj_t *scr, const char *title, int backTo) {
  lv_obj_t *r = trow(scr, 13, 11);
  mklabel(r, U_SPARK " ", F14, C_ACCENT);
  mklabel(r, title, F14, C_TEXT);
  if (backTo >= 0)
    tbtn(scr, 378, 5, 89, 32, TRS(U_LEFT " indietro", U_LEFT " back"), F14, C_MUTED, C_BORDER, nav_cb, (void *)(intptr_t)backTo);
  hline(scr, 13, 42, 454, C_BORDER);
}
// riga chiave/valore toccabile (impostazioni, modelli, reti wifi)
static lv_obj_t *kv_row(lv_obj_t *list, const char *key, const char *val, uint32_t keyCol, uint32_t valCol,
                        lv_event_cb_t cb, void *ud, lv_obj_t **valOut = nullptr) {
  lv_obj_t *r = plain_obj(list);
  lv_obj_set_size(r, 454, 42);
  lv_obj_add_flag(r, LV_OBJ_FLAG_CLICKABLE);
  lv_obj_set_style_bg_color(r, lv_color_hex(C_SURFACE), LV_STATE_PRESSED);
  lv_obj_set_style_bg_opa(r, LV_OPA_COVER, LV_STATE_PRESSED);
  lv_obj_t *k = mklabel(r, key, F14, keyCol);
  lv_obj_align(k, LV_ALIGN_LEFT_MID, 13, 0);
  lv_obj_t *v = mklabel(r, val, F14, valCol);
  lv_obj_set_width(v, 230);
  lv_label_set_long_mode(v, LV_LABEL_LONG_DOT);
  lv_obj_set_style_text_align(v, LV_TEXT_ALIGN_RIGHT, 0);
  lv_obj_align(v, LV_ALIGN_RIGHT_MID, -13, 0);
  static lv_point_precise_t PTS_W454[2] = {{0, 0}, {454, 0}};
  dline(r, 0, 41, PTS_W454);
  if (cb) lv_obj_add_event_cb(r, cb, LV_EVENT_CLICKED, ud);
  if (valOut) *valOut = v;
  return r;
}
static lv_obj_t *tlist(lv_obj_t *scr, int x, int y, int w, int h) {
  lv_obj_t *l = plain_obj(scr);
  lv_obj_set_pos(l, x, y); lv_obj_set_size(l, w, h);
  lv_obj_set_flex_flow(l, LV_FLEX_FLOW_COLUMN);
  lv_obj_add_flag(l, LV_OBJ_FLAG_SCROLLABLE);
  lv_obj_set_scroll_dir(l, LV_DIR_VER);
  lv_obj_set_scrollbar_mode(l, LV_SCROLLBAR_MODE_AUTO);
  lv_obj_set_style_bg_color(l, lv_color_hex(C_FAINT), LV_PART_SCROLLBAR);
  lv_obj_set_style_bg_opa(l, LV_OPA_COVER, LV_PART_SCROLLBAR);
  lv_obj_set_style_width(l, 3, LV_PART_SCROLLBAR);
  return l;
}
// campo di testo e tastiera scuri (prima: tema chiaro di default di LVGL)
static void style_ta(lv_obj_t *ta) {
  lv_obj_set_style_bg_color(ta, lv_color_hex(C_SURFACE), 0);
  lv_obj_set_style_text_color(ta, lv_color_hex(C_TEXT), 0);
  lv_obj_set_style_text_font(ta, F14, 0);
  lv_obj_set_style_border_width(ta, 1, 0);
  lv_obj_set_style_border_color(ta, lv_color_hex(C_BORDER), 0);
  lv_obj_set_style_border_color(ta, lv_color_hex(C_ACCENT), LV_STATE_FOCUSED);
  lv_obj_set_style_radius(ta, 4, 0);
  lv_obj_set_style_pad_hor(ta, 12, 0);
  lv_obj_set_style_text_color(ta, lv_color_hex(C_FAINT), LV_PART_TEXTAREA_PLACEHOLDER);
  lv_obj_set_style_border_color(ta, lv_color_hex(C_ACCENT), LV_PART_CURSOR | LV_STATE_FOCUSED);
  lv_obj_set_style_shadow_width(ta, 0, 0);
}
static void style_kb(lv_obj_t *kb) {
  lv_obj_set_style_bg_color(kb, lv_color_hex(C_BG), 0);
  lv_obj_set_style_border_width(kb, 1, 0);
  lv_obj_set_style_border_side(kb, LV_BORDER_SIDE_TOP, 0);
  lv_obj_set_style_border_color(kb, lv_color_hex(C_BORDER), 0);
  lv_obj_set_style_pad_all(kb, 6, 0);
  lv_obj_set_style_pad_gap(kb, 4, 0);
  lv_obj_set_style_radius(kb, 0, 0);
  lv_obj_set_style_bg_color(kb, lv_color_hex(C_SURFACE), LV_PART_ITEMS);
  lv_obj_set_style_text_color(kb, lv_color_hex(C_TEXT), LV_PART_ITEMS);
  lv_obj_set_style_text_font(kb, F14, LV_PART_ITEMS);
  lv_obj_set_style_border_width(kb, 1, LV_PART_ITEMS);
  lv_obj_set_style_border_color(kb, lv_color_hex(C_TRACK), LV_PART_ITEMS);
  lv_obj_set_style_radius(kb, 3, LV_PART_ITEMS);
  lv_obj_set_style_shadow_width(kb, 0, LV_PART_ITEMS);
  lv_obj_set_style_bg_color(kb, lv_color_hex(C_SURFACE2), LV_PART_ITEMS | LV_STATE_PRESSED);
  lv_obj_set_style_bg_color(kb, lv_color_hex(C_BG), LV_PART_ITEMS | LV_STATE_CHECKED);
  lv_obj_set_style_text_color(kb, lv_color_hex(C_MUTED), LV_PART_ITEMS | LV_STATE_CHECKED);
  lv_obj_set_style_border_color(kb, lv_color_hex(C_BORDER), LV_PART_ITEMS | LV_STATE_CHECKED);
}
// spinner di Claude Code (· ✢ ✳ ✶ ✻ ✽ avanti e indietro): una label, 1 carattere
static const char *SPIN[10] = {"\xC2\xB7", "\xE2\x9C\xA2", "\xE2\x9C\xB3", "\xE2\x9C\xB6", "\xE2\x9C\xBB",
                               "\xE2\x9C\xBD", "\xE2\x9C\xBB", "\xE2\x9C\xB6", "\xE2\x9C\xB3", "\xE2\x9C\xA2"};
static lv_obj_t *g_spin = nullptr;
static void spin_tick() {
  static uint32_t last = 0; static int k = 0;
  if (!g_spin) return;
  uint32_t now = millis();
  if (now - last < 120) return;
  last = now; k = (k + 1) % 10;
  lv_label_set_text(g_spin, SPIN[k]);
}
// riga "✻ testo" centrata con lo spinner che gira
static lv_obj_t *spin_row(lv_obj_t *scr, const char *txt, int yOfs) {
  lv_obj_t *r = plain_obj(scr);
  lv_obj_set_size(r, LV_SIZE_CONTENT, LV_SIZE_CONTENT);
  lv_obj_set_flex_flow(r, LV_FLEX_FLOW_ROW);
  lv_obj_set_flex_align(r, LV_FLEX_ALIGN_START, LV_FLEX_ALIGN_CENTER, LV_FLEX_ALIGN_CENTER);
  lv_obj_set_style_pad_column(r, 8, 0);
  g_spin = mklabel(r, SPIN[0], F14, C_ACCENT);
  lv_obj_t *t = mklabel(r, txt, F14, C_TEXT);
  lv_obj_align(r, LV_ALIGN_CENTER, 0, yOfs);
  return t;
}
// "reset tra 1h 23m" / "2d 4h" / "ora" / "--" (orologio non sincronizzato)
static void fmt_eta(uint32_t epoch, char *out, int sz) {
  time_t now = time(nullptr);
  if (now < 1000000000L || epoch == 0) { snprintf(out, sz, "--"); return; }
  long d = (long)epoch - (long)now;
  if (d <= 0) { snprintf(out, sz, "%s", TRS("ora", "now")); return; }
  int days = d / 86400; d %= 86400;
  int hrs  = d / 3600;  d %= 3600;
  int mins = d / 60;
  if (days > 0)      snprintf(out, sz, "%dd %dh", days, hrs);
  else if (hrs > 0)  snprintf(out, sz, "%dh %02dm", hrs, mins);
  else               snprintf(out, sz, "%dm", mins);
}
static void fmt_clock(uint32_t epoch, char *out, int sz) {
  if (epoch == 0 || time(nullptr) < 1000000000L) { strlcpy(out, "--:--", sz); return; }
  time_t t = (time_t)epoch; struct tm tmv;
  localtime_r(&t, &tmv);
  if (!g_lang) {                         // %a e' sempre in inglese (locale C)
    static const char *GG[7] = {"Dom", "Lun", "Mar", "Mer", "Gio", "Ven", "Sab"};
    snprintf(out, sz, "%s %02d:%02d", GG[tmv.tm_wday % 7], tmv.tm_hour, tmv.tm_min);
    return;
  }
  strftime(out, sz, "%a %H:%M", &tmv);
}
static void fmt_hm(uint32_t epoch, char *out, int sz) {
  if (epoch == 0 || time(nullptr) < 1000000000L) { strlcpy(out, "--:--", sz); return; }
  time_t t = (time_t)epoch; struct tm tmv;
  localtime_r(&t, &tmv);
  strftime(out, sz, "%H:%M", &tmv);
}
// 1234 -> "1.2k", 2345678 -> "2.3M"

// ============================================================
// NVS / persistenza
// ============================================================
static void load_persisted() {
  g_prefs.begin(NVS_NAMESPACE, false);
  accountsLoad(g_prefs, g_accts);
  if (g_accts.used[g_accts.active] &&
      accountLoadBlob(g_prefs, g_accts.active, g_blob)) {
    g_hasToken = true;
  }
  g_pinAttempts = g_prefs.getInt("pinatt", 0);
  g_briIdx = g_prefs.getInt("bri", 1);
  g_autoBri = g_prefs.getInt("autobri", 0);
  if (g_autoBri < 0 || g_autoBri > 3) g_autoBri = 0;
  g_ssTab = g_prefs.getBool("sstab", true);
  {                                                  // ordine delle pagine: valido solo se e' una permutazione con la home prima
    uint8_t o[NTILES];
    if (g_prefs.getBytes("porder", o, NTILES) == NTILES && o[0] == PG_HOME) {
      uint8_t seen = 0; bool ok = true;
      for (int i = 0; i < NTILES; i++) { if (o[i] >= NTILES || (seen >> o[i]) & 1) ok = false; else seen |= 1 << o[i]; }
      if (ok) memcpy(g_pageOrder, o, NTILES);
    }
  }
  g_brkIdx = g_prefs.getInt("brk", 0);
  if (g_brkIdx < 0 || g_brkIdx > 3) g_brkIdx = 0;
  g_wkAlIdx = g_prefs.getInt("wkal", 2);
  if (g_wkAlIdx < 0 || g_wkAlIdx > 3) g_wkAlIdx = 2;
  g_wkAlDone = g_prefs.getUInt("wkald", 0);
  g_shBtn = (uint16_t)g_prefs.getUInt("shbtn", 0x0F);
  if (!g_shBtn || g_shBtn >= (1 << SHB_N)) g_shBtn = 0x0F;
  g_ccDay = g_prefs.getLong("ccd", 0);
  g_ccN = g_prefs.getInt("ccn", 0);
  g_ccT = g_prefs.getUInt("cct", 0);
  g_ccX = g_prefs.getUInt("ccx", 0);
  g_mediaAuto = g_prefs.getBool("mauto", true);
  cd_load();
  if (g_briIdx < 0 || g_briIdx > 2) g_briIdx = 1;
  g_pollSec = g_prefs.getInt("poll", DEFAULT_POLL_SEC);
  if (g_pollSec < MIN_POLL_SEC || g_pollSec > MAX_POLL_SEC) g_pollSec = DEFAULT_POLL_SEC;
  g_tzOffset = g_prefs.getInt("tz", TZ_ROME);
  if (g_tzOffset != TZ_ROME && (g_tzOffset < -12 || g_tzOffset > 14)) g_tzOffset = TZ_ROME;
  g_slideSec = g_prefs.getInt("slide", 0);
  if (g_slideSec != 0 && g_slideSec != 5 && g_slideSec != 10 &&
      g_slideSec != 15 && g_slideSec != 30) g_slideSec = 0;
  g_heatMode = g_prefs.getInt("heatm", 3);
  g_heatSrc = g_prefs.getInt("heats", 0) ? 1 : 0;
  g_perfOn = g_prefs.getBool("perf", false);
  g_resetAlert = g_prefs.getBool("rstal", true);
  g_pomoToday = g_prefs.getInt("pomn", 0);
  g_pomoDay = g_prefs.getLong("pomday", 0);
  g_pcSound = g_prefs.getBool("pcsnd", true);
  g_ccFocusDefer = g_prefs.getBool("ccfocus", false);
  strlcpy(g_ical, g_prefs.getString("ical", "").c_str(), sizeof(g_ical));
  g_calAlIdx = g_prefs.getInt("calal", 1);
  if (g_calAlIdx < 0 || g_calAlIdx > 3) g_calAlIdx = 1;
  g_ccCloseIdx = g_prefs.getInt("ccclose", 2);
  if (g_ccCloseIdx < 0 || g_ccCloseIdx > 3) g_ccCloseIdx = 2;
  g_ccAlert = g_prefs.getInt("ccal", 2);
  if (g_ccAlert < 0 || g_ccAlert > 3) g_ccAlert = 2;
  g_nightIdx = g_prefs.getInt("night", 0);
  if (g_nightIdx < 0 || g_nightIdx > 3) g_nightIdx = 0;
  g_nightPause = g_prefs.getBool("nightp", true);
  g_nightClock = g_prefs.getBool("nightclk", true);
  g_nightBri = g_prefs.getInt("nightbri", 0) ? 1 : 0;
  g_userPause = g_prefs.getBool("pause", false);
  g_pauseUntil = g_prefs.getUInt("pauseu", 0);
  g_clockIdx = g_prefs.getInt("clock", 0);
  g_pcIntIdx = g_prefs.getInt("pcint", 0);
  g_kwhPrice = g_prefs.getFloat("kwh", 0.30f);
  if (g_pcIntIdx < 0 || g_pcIntIdx > 3) g_pcIntIdx = 0;
  g_wxLat = g_prefs.getFloat("wxlat", DEFAULT_WX_LAT);
  g_wxLon = g_prefs.getFloat("wxlon", DEFAULT_WX_LON);
  strlcpy(g_wxCity, g_prefs.getString("wxcity", DEFAULT_WX_CITY).c_str(), sizeof(g_wxCity));
  strlcpy(g_pcHost, g_prefs.getString("pchost", DEFAULT_PC_HOST).c_str(), sizeof(g_pcHost));
  if (g_clockIdx < 0 || g_clockIdx > 3) g_clockIdx = 0;
  g_dimIdx = g_prefs.getInt("dim", 0);
  if (g_dimIdx < 0 || g_dimIdx > 3) g_dimIdx = 0;
  if (g_heatMode < 0 || g_heatMode > 3) g_heatMode = 3;
  g_lang = g_prefs.getInt("lang", 0) ? 1 : 0;
  models_load();
}
static void save_attempts() { g_prefs.putInt("pinatt", g_pinAttempts); }
static void apply_brightness() { if (g_screenMode == 0) ledcWrite(TFT_BL, BRI_LEVELS[g_briIdx]); }
static void screen_apply() {
  ledcWrite(TFT_BL, g_screenMode == 2 ? 0 : g_screenMode == 3 ? NIGHT_BRI[g_nightBri]
                    : (g_screenMode == 1 ? DIM_LEVEL : BRI_LEVELS[g_briIdx]));
}
// luminosita' automatica: al cambio giorno/sera imposta alta o bassa. Un tocco manuale vale
// fino al passaggio successivo; il livello scelto a mano in NVS non viene toccato.
static int hm_min(const char *hm, int dflt) {
  int h, m;
  if (!hm || sscanf(hm, "%d:%d", &h, &m) != 2 || h < 0 || h > 23 || m < 0 || m > 59) return dflt;
  return h * 60 + m;
}
static int g_autoBriPhase = -1;                      // -1 da ricalcolare, 0 giorno, 1 sera
static void auto_bri_tick(bool force) {
  static uint32_t last = 0;
  if (!force && millis() - last < 30000) return;
  last = millis();
  if (!g_autoBri) { g_autoBriPhase = -1; return; }
  time_t now = time(nullptr);
  if (now < 1000000000L) return;
  struct tm tv; localtime_r(&now, &tv);
  int cur = tv.tm_hour * 60 + tv.tm_min;
  int from = 20 * 60, to = 7 * 60;
  if (g_autoBri == 1 && g_wx.ok) { from = hm_min(g_wx.sunset, from); to = hm_min(g_wx.sunrise, to); }
  else if (g_autoBri == 3) from = 21 * 60;
  int phase = (cur >= from || cur < to) ? 1 : 0;
  if (phase == g_autoBriPhase && !force) return;
  g_autoBriPhase = phase;
  g_briIdx = phase ? 0 : 2;
  apply_brightness();
  Serial.printf("[SCREEN] luminosita' automatica: %s\n", phase ? "sera (bassa)" : "giorno (alta)");
}

// true se l'ora locale e' nella fascia notte scelta (fino alle 7:00)
static bool night_active() {
  if (!g_nightIdx) return false;
  time_t now = time(nullptr);
  if (now < 1000000000L) return false;
  struct tm tv; localtime_r(&now, &tv);
  int from = NIGHT_FROM[g_nightIdx];
  return from == 0 ? tv.tm_hour < 7 : (tv.tm_hour >= from || tv.tm_hour < 7);
}
static bool night_paused() { return g_nightPause && night_active(); }
// avviso al PC collegato (suono e notifica di Windows via Ritmo Code PC Monitor); di notte niente
static void pc_notify(const char *ev, const char *title, const char *msg) {
  if (!g_pcSound || !g_pcHost[0] || !ev[0] || night_active()) return;
  strlcpy(g_pcNtf.host, g_pcHost, sizeof(g_pcNtf.host));
  strlcpy(g_pcNtf.ev, ev, sizeof(g_pcNtf.ev));
  strlcpy(g_pcNtf.title, title, sizeof(g_pcNtf.title));
  strlcpy(g_pcNtf.msg, msg, sizeof(g_pcNtf.msg));
  g_pcNtfReq = true;
}
// niente richieste automatiche: pausa manuale o notte (il tasto ↻ aggiorna comunque)
static bool polling_paused() { return g_userPause || night_paused(); }
// Orologio notturno a tutto schermo (variante B): ora grande in grigio caldo, data e riepilogo
struct NightClockUI { lv_obj_t *scrim, *time, *date, *info; int lastMin; };
static NightClockUI g_nc = {};
static void night_clock_close() { if (g_nc.scrim) { lv_obj_delete(g_nc.scrim); memset(&g_nc, 0, sizeof(g_nc)); } }
static void night_clock_update(bool force) {
  if (!g_nc.scrim) return;
  time_t now = time(nullptr);
  if (now < 1000000000L) return;
  struct tm tv; localtime_r(&now, &tv);
  if (!force && tv.tm_min == g_nc.lastMin) return;
  g_nc.lastMin = tv.tm_min;
  char s[80];
  snprintf(s, sizeof(s), "%02d:%02d", tv.tm_hour, tv.tm_min);
  lv_label_set_text(g_nc.time, s);
  static const char *GIT[7] = {"domenica", "luned\xC3\xAC", "marted\xC3\xAC", "mercoled\xC3\xAC", "gioved\xC3\xAC", "venerd\xC3\xAC", "sabato"};
  static const char *GEN[7] = {"sunday", "monday", "tuesday", "wednesday", "thursday", "friday", "saturday"};
  static const char *MIT[12] = {"gennaio", "febbraio", "marzo", "aprile", "maggio", "giugno", "luglio", "agosto", "settembre", "ottobre", "novembre", "dicembre"};
  static const char *MEN[12] = {"january", "february", "march", "april", "may", "june", "july", "august", "september", "october", "november", "december"};
  if (g_lang) snprintf(s, sizeof(s), "%s, %s %d", GEN[tv.tm_wday], MEN[tv.tm_mon], tv.tm_mday);
  else        snprintf(s, sizeof(s), "%s %d %s", GIT[tv.tm_wday], tv.tm_mday, MIT[tv.tm_mon]);
  lv_label_set_text(g_nc.date, s);
  int n = 0; s[0] = 0;
  if (g_usage.ok) n += snprintf(s + n, sizeof(s) - n, TRS("5h %.0f%% " U_MIDDOT " sett. %.0f%%", "5h %.0f%% " U_MIDDOT " week %.0f%%"), g_usage.h5, g_usage.d7);
  if (g_wx.ok) {
    n += snprintf(s + n, sizeof(s) - n, "%s%.0f\xC2\xB0", n ? " " U_MIDDOT " " : "", g_wx.temp);
    for (int i = 0; i < 12; i++)
      if (g_wx.rain[i] >= 40) { snprintf(s + n, sizeof(s) - n, TRS(" pioggia alle %02d", " rain at %02d"), (g_wx.rainHour0 + i) % 24); break; }
  }
  lv_label_set_text(g_nc.info, s);
}
static void night_clock_show() {
  night_clock_close();
  lv_obj_t *s = lv_obj_create(lv_layer_top());
  lv_obj_remove_style_all(s);
  g_nc.scrim = s;
  lv_obj_set_size(s, 480, 320);
  lv_obj_set_style_bg_color(s, lv_color_hex(0x000000), 0);
  lv_obj_set_style_bg_opa(s, LV_OPA_COVER, 0);
  lv_obj_add_flag(s, LV_OBJ_FLAG_CLICKABLE);             // i tocchi non arrivano al dashboard sotto
  g_nc.time = lv_label_create(s);
  lv_obj_set_style_text_font(g_nc.time, F150, 0);
  lv_obj_set_style_text_color(g_nc.time, lv_color_hex(0xA8A49A), 0);
  lv_obj_align(g_nc.time, LV_ALIGN_CENTER, 0, -38);   // centro su y 122 = 320 / phi^2
  g_nc.date = lv_label_create(s);
  lv_obj_set_style_text_font(g_nc.date, F14, 0);
  lv_obj_set_style_text_color(g_nc.date, lv_color_hex(0x5C5A55), 0);
  lv_obj_align(g_nc.date, LV_ALIGN_CENTER, 0, 49);    // parte da y 199 ~ 320 / phi
  g_nc.info = lv_label_create(s);
  lv_obj_set_style_text_font(g_nc.info, F12, 0);
  lv_obj_set_style_text_color(g_nc.info, lv_color_hex(0x5C5A55), 0);
  lv_obj_align(g_nc.info, LV_ALIGN_BOTTOM_MID, 0, -21);
  g_nc.lastMin = -1;
  night_clock_update(true);
  lv_obj_align(g_nc.time, LV_ALIGN_CENTER, 0, -38);       // ricentra con il testo reale
  lv_obj_align(g_nc.date, LV_ALIGN_CENTER, 0, 49);    // parte da y 199 ~ 320 / phi
  lv_obj_align(g_nc.info, LV_ALIGN_BOTTOM_MID, 0, -21);
}
// allinea l'overlay allo stato dello schermo (fuori dalla callback del touch, dove non si toccano oggetti)
static void night_clock_sync() {
  if (g_screenMode == 3 && !g_nc.scrim) night_clock_show();
  else if (g_screenMode != 3 && g_nc.scrim) night_clock_close();
  if (g_nc.scrim) {
    static uint32_t last = 0;
    if (millis() - last > 1000) { last = millis(); night_clock_update(false); }
  }
}

// Stato dello schermo (ogni ~500 ms): notte -> orologio tenue o spento dopo 30 s senza tocchi,
// attenuazione -> dopo N minuti. Fuori dal dashboard resta sempre acceso.
static void screen_tick() {
  static uint32_t last = 0;
  if (millis() - last < 500) return;
  last = millis();
  uint32_t idle = millis() - g_lastTouchMs;
  uint8_t want = 0;
  if (g_state == ST_MAIN) {
    if (night_active() && idle > NIGHT_WAKE_MS) want = g_nightClock ? 3 : 2;
    else if (g_dimIdx && idle > DIM_MIN[g_dimIdx] * 60000UL) want = 1;
  }
  if (want != g_screenMode) {
    g_screenMode = want;
    screen_apply();
    Serial.printf("[SCREEN] %s\n", want == 3 ? "orologio (notte)" : want == 2 ? "spento (notte)" : want == 1 ? "attenuato" : "acceso");
  }
}

static void reset_history_ram();

static void factory_reset() {
  g_dataEpoch++;
  g_prefs.clear();              // cancella blob, pinatt, bri dal namespace claude
  for (int i = 0; i < NMODELS; i++) {         // gli ID personalizzati erano in NVS: torna ai predefiniti
    strlcpy(g_models[i].id, g_models[i].defId, MODEL_ID_MAX);
    g_models[i].pr.code = 0; g_models[i].pr.ms = 0; g_models[i].pr.msg[0] = 0;
  }
  g_wifi.forgetAll();
  for (int i = 0; i < ACCT_MAX; i++) {
    char pth[16]; snprintf(pth, sizeof(pth), "/hist%d.bin", i);
    LittleFS.remove(pth);
    snprintf(pth, sizeof(pth), "/weeks%d.bin", i);
    LittleFS.remove(pth);
  }
  memset(&g_accts, 0, sizeof(g_accts));
  memset(g_sessionPin, 0, sizeof(g_sessionPin));
  g_pendingLabel[0] = 0;
  g_tokenTargetSlot = 0;
  reset_history_ram();
  g_hasToken = false;
  g_token[0] = 0; g_pendingToken[0] = 0;
  g_pinAttempts = 0;
  g_onboarding = true;
  Serial.println("[RESET] tutto cancellato");
}

// ============================================================
// Schermata: PIN (tastierino touch) — inserisce il PIN per decifrare OPPURE ne imposta uno nuovo nel setup
// ============================================================
static const char *pin_map[] = {
  "1", "2", "3", "\n",
  "4", "5", "6", "\n",
  "7", "8", "9", "\n",
  U_BKSP, "0", U_ENTER, ""
};

static void pin_update_dots() {
  if (!g_pinDots) return;
  char dots[32] = {0};
  int len = strlen(g_pinEntry);
  strcat(dots, "[ ");
  for (int i = 0; i < PIN_LEN; i++) {
    strcat(dots, i < len ? "*" : "_");
    strcat(dots, " ");
  }
  strcat(dots, "]");
  lv_label_set_text(g_pinDots, dots);
}

static void pin_submit() {
  if (g_state == ST_SETUP_PIN) {
    if (!g_pinConfirming) {
      strlcpy(g_pinFirst, g_pinEntry, sizeof(g_pinFirst));
      g_pinConfirming = true;
      g_pinEntry[0] = 0;
      pin_update_dots();
      if (g_pinMsg) lv_label_set_text(g_pinMsg, TRS("Conferma il PIN", "Confirm the PIN"));
      return;
    }
    // conferma
    if (strcmp(g_pinFirst, g_pinEntry) != 0) {
      g_pinConfirming = false;
      g_pinFirst[0] = 0; g_pinEntry[0] = 0;
      pin_update_dots();
      if (g_pinMsg) lv_label_set_text(g_pinMsg, TRS("Non coincide. Reimpostalo.", "Didn't match. Set it again."));
      return;
    }
    // PIN impostato -> cifra il token in sospeso e salva
    if (!encryptToken(g_pendingToken, g_pinEntry, g_blob)) {
      if (g_pinMsg) lv_label_set_text(g_pinMsg, TRS("Cifratura fallita. Riprova.", "Encryption failed. Try again."));
      g_pinConfirming = false; g_pinFirst[0] = 0; g_pinEntry[0] = 0; pin_update_dots();
      return;
    }
    accountSave(g_prefs, g_accts, g_tokenTargetSlot, g_blob, g_pendingLabel);
    accountSetActive(g_prefs, g_accts, g_tokenTargetSlot);
    g_pendingLabel[0] = 0;
    strlcpy(g_sessionPin, g_pinEntry, sizeof(g_sessionPin));
    strlcpy(g_token, g_pendingToken, sizeof(g_token));
    memset(g_pendingToken, 0, sizeof(g_pendingToken));
    g_hasToken = true; g_onboarding = false;
    g_pinAttempts = 0; save_attempts();
    g_pinConfirming = false;
    memset(g_pinFirst, 0, sizeof(g_pinFirst));   // azzera davvero: le cifre restano
    memset(g_pinEntry, 0, sizeof(g_pinEntry));   // in RAM se si pulisce solo [0]
    Serial.println("[PIN] token cifrato e salvato");
    request_state(g_wifi.isConnected() ? ST_LOADING : ST_WIFI);
    return;
  }

  // conferma di "cancella tutto": serve il PIN di questa sessione
  if (g_pinForWipe) {
    char tmp[sizeof(g_token)];
    bool ok = g_sessionPin[0] ? strcmp(g_pinEntry, g_sessionPin) == 0
                              : decryptToken(g_blob, g_pinEntry, tmp, sizeof(tmp));
    memset(tmp, 0, sizeof(tmp));
    memset(g_pinEntry, 0, sizeof(g_pinEntry));
    if (ok) {
      Serial.println("[PIN] cancella tutto confermato");
      g_pinForWipe = false;
      factory_reset();
      request_state(ST_WIFI);
    } else {
      pin_update_dots();
      if (g_pinMsg) { lv_label_set_text(g_pinMsg, TRS("PIN errato: niente cancellato", "Wrong PIN: nothing erased")); }
    }
    return;
  }

  // ST_PIN: prova a decifrare
  if (decryptToken(g_blob, g_pinEntry, g_token, sizeof(g_token))) {
    g_pinAttempts = 0; save_attempts();
    strlcpy(g_sessionPin, g_pinEntry, sizeof(g_sessionPin));
    memset(g_pinEntry, 0, sizeof(g_pinEntry));
    Serial.printf("[PIN] ok, token %d chars\n", (int)strlen(g_token));
    if (!g_wifi.isConnected()) g_wifi.autoConnect(WIFI_CONNECT_TIMEOUT_MS);
    request_state(g_wifi.isConnected() ? ST_LOADING : ST_WIFI);
  } else {
    g_pinAttempts++; save_attempts();
    g_pinEntry[0] = 0; pin_update_dots();
    if (g_pinAttempts >= MAX_PIN_ATTEMPTS) {
      Serial.println("[PIN] limite superato -> wipe");
      factory_reset();
      request_state(ST_WIFI);
      return;
    }
    int wait = LOCKOUT_SEC;
    g_lockoutUntil = millis() + (uint32_t)wait * 1000;
    if (g_pinMsg) {
      char m[64];
      snprintf(m, sizeof(m), TRS("PIN errato (%d/%d). Attendi %ds", "Wrong PIN (%d/%d). Wait %ds"),
               g_pinAttempts, MAX_PIN_ATTEMPTS, wait);
      lv_label_set_text(g_pinMsg, m);
    }
  }
}

static void pin_kb_cb(lv_event_t *e) {
  if (lv_event_get_code(e) != LV_EVENT_VALUE_CHANGED) return;
  if (millis() < g_lockoutUntil) return;     // bloccato
  lv_obj_t *bm = (lv_obj_t *)lv_event_get_target(e);
  uint32_t id = lv_buttonmatrix_get_selected_button(bm);
  const char *txt = lv_buttonmatrix_get_button_text(bm, id);
  if (!txt) return;
  int len = strlen(g_pinEntry);
  if (strcmp(txt, U_BKSP) == 0) {
    if (len > 0) g_pinEntry[len - 1] = 0;
    pin_update_dots();
  } else if (strcmp(txt, U_ENTER) == 0) {
    if (len == PIN_LEN) pin_submit();
  } else if (len < PIN_LEN) {
    g_pinEntry[len] = txt[0];
    g_pinEntry[len + 1] = 0;
    pin_update_dots();
    if (len + 1 == PIN_LEN) pin_submit();     // invio automatico al completamento
  }
}

static void wipe_cancel_cb(lv_event_t *e) {
  (void)e;
  g_pinForWipe = false;
  memset(g_pinEntry, 0, sizeof(g_pinEntry));
  request_state(ST_SETTINGS);
}
static void ui_pin() {
  lv_obj_t *scr = lv_screen_active();
  const char *title = (g_state == ST_SETUP_PIN)
    ? (g_pinConfirming ? TRS("conferma il PIN", "confirm the PIN") : TRS("imposta un PIN", "set a PIN"))
    : g_pinForWipe ? TRS("PIN per cancellare tutto", "PIN to erase everything")
    : TRS("inserisci il PIN", "enter the PIN");
  lv_obj_t *r = plain_obj(scr);
  lv_obj_set_size(r, LV_SIZE_CONTENT, LV_SIZE_CONTENT);
  lv_obj_set_flex_flow(r, LV_FLEX_FLOW_ROW);
  mklabel(r, U_SPARK " ", F14, C_ACCENT);
  mklabel(r, title, F14, C_TEXT);
  lv_obj_align(r, LV_ALIGN_TOP_MID, 0, 12);

  g_pinDots = mklabel(scr, "", F22, C_ACCENT);
  lv_obj_align(g_pinDots, LV_ALIGN_TOP_MID, 0, 40);
  pin_update_dots();

  const char *sub = (g_state == ST_SETUP_PIN)
    ? TRS("lo inserirai a ogni avvio", "you'll type it on every boot")
    : g_pinForWipe ? TRS("token, account, reti e storico verranno cancellati", "token, accounts, networks and history will be erased")
    : TRS("serve per sbloccare il token", "needed to unlock the token");
  g_pinMsg = mklabel(scr, sub, F12, g_pinForWipe ? C_BAD : C_MUTED);
  if (g_pinForWipe)                               // si torna alle impostazioni senza cancellare
    tbtn(scr, 378, 5, 89, 32, TRS(U_LEFT " annulla", U_LEFT " cancel"), F14, C_MUTED, C_BORDER, wipe_cancel_cb, NULL);
  lv_obj_align(g_pinMsg, LV_ALIGN_TOP_MID, 0, 80);

  lv_obj_t *bm = lv_buttonmatrix_create(scr);
  lv_buttonmatrix_set_map(bm, pin_map);
  lv_obj_set_size(bm, 260, 200);
  lv_obj_align(bm, LV_ALIGN_BOTTOM_MID, 0, -8);
  lv_obj_set_style_bg_opa(bm, 0, 0);
  lv_obj_set_style_border_width(bm, 0, 0);
  lv_obj_set_style_pad_all(bm, 0, 0);
  lv_obj_set_style_pad_gap(bm, 6, 0);
  lv_obj_set_style_text_font(bm, F22, LV_PART_ITEMS);
  lv_obj_set_style_bg_opa(bm, 0, LV_PART_ITEMS);
  lv_obj_set_style_bg_color(bm, lv_color_hex(C_SURFACE2), LV_PART_ITEMS | LV_STATE_PRESSED);
  lv_obj_set_style_bg_opa(bm, LV_OPA_COVER, LV_PART_ITEMS | LV_STATE_PRESSED);
  lv_obj_set_style_border_width(bm, 1, LV_PART_ITEMS);
  lv_obj_set_style_border_color(bm, lv_color_hex(C_BORDER), LV_PART_ITEMS);
  lv_obj_set_style_radius(bm, 4, LV_PART_ITEMS);
  lv_obj_set_style_shadow_width(bm, 0, LV_PART_ITEMS);
  lv_obj_set_style_text_color(bm, lv_color_hex(C_TEXT), LV_PART_ITEMS);
  lv_obj_add_event_cb(bm, pin_kb_cb, LV_EVENT_VALUE_CHANGED, NULL);

  if (millis() < g_lockoutUntil && g_pinMsg) {
    int rem = (g_lockoutUntil - millis()) / 1000;
    char m[48]; snprintf(m, sizeof(m), TRS("attendi %ds", "wait %ds"), rem);
    lv_label_set_text(g_pinMsg, m);
  }
}

// ============================================================
// Schermata: WiFi (scan + tastiera)
// ============================================================
static lv_obj_t *wifi_list = nullptr, *wifi_ta = nullptr, *wifi_kb = nullptr, *wifi_status = nullptr;
static char sel_ssid[33] = {0};
static WiFiManager::NetworkInfo g_nets[12];
static void wifi_item_cb(lv_event_t *e);

static void wifi_populate() {
  lv_obj_clean(wifi_list);
  lv_label_set_text(wifi_status, TRS("ricerca reti...", "scanning networks..."));
  lv_refr_now(NULL);
  int n = g_wifi.scanNetworks(g_nets, 12);
  for (int i = 0; i < n; i++) {
    const char *sig = g_nets[i].rssi > -55 ? "\xE2\x96\x82\xE2\x96\x84\xE2\x96\x86\xE2\x96\x88"
                    : g_nets[i].rssi > -67 ? "\xE2\x96\x82\xE2\x96\x84\xE2\x96\x86"
                    : g_nets[i].rssi > -78 ? "\xE2\x96\x82\xE2\x96\x84" : "\xE2\x96\x82";
    kv_row(wifi_list, g_nets[i].ssid, sig, C_TEXT, C_ACCENT, wifi_item_cb, (void *)(intptr_t)i);
  }
  lv_label_set_text(wifi_status, n > 0 ? TRS("tocca la tua rete", "tap your network")
                                       : TRS("nessuna rete: tocca cerca", "no networks: tap scan"));
}
static void wifi_item_cb(lv_event_t *e) {
  int i = (int)(intptr_t)lv_event_get_user_data(e);
  if (i < 0 || i >= 12) return;
  strlcpy(sel_ssid, g_nets[i].ssid, sizeof(sel_ssid));
  lv_label_set_text_fmt(wifi_status, TRS("password di \"%s\":", "password for \"%s\":"), sel_ssid);
  lv_obj_add_flag(wifi_list, LV_OBJ_FLAG_HIDDEN);
  lv_textarea_set_text(wifi_ta, "");
  lv_obj_clear_flag(wifi_ta, LV_OBJ_FLAG_HIDDEN);
  lv_obj_clear_flag(wifi_kb, LV_OBJ_FLAG_HIDDEN);
  lv_keyboard_set_textarea(wifi_kb, wifi_ta);
}
static void wifi_kb_cb(lv_event_t *e) {
  lv_event_code_t code = lv_event_get_code(e);
  if (code == LV_EVENT_READY) {
    const char *pass = lv_textarea_get_text(wifi_ta);
    lv_label_set_text(wifi_status, TRS("connessione...", "connecting..."));
    lv_obj_add_flag(wifi_kb, LV_OBJ_FLAG_HIDDEN);
    lv_obj_add_flag(wifi_ta, LV_OBJ_FLAG_HIDDEN);
    lv_refr_now(NULL);
    bool ok = g_wifi.connectTo(sel_ssid, pass, 15000);
    if (ok) request_state(g_onboarding ? ST_TOKEN : ST_LOADING);
    else {
      lv_label_set_text(wifi_status, TRS("non riuscito: tocca di nuovo una rete", "failed: tap a network again"));
      lv_obj_clear_flag(wifi_list, LV_OBJ_FLAG_HIDDEN);
    }
  } else if (code == LV_EVENT_CANCEL) {
    lv_obj_add_flag(wifi_kb, LV_OBJ_FLAG_HIDDEN);
    lv_obj_add_flag(wifi_ta, LV_OBJ_FLAG_HIDDEN);
    lv_obj_clear_flag(wifi_list, LV_OBJ_FLAG_HIDDEN);
    lv_label_set_text(wifi_status, TRS("tocca la tua rete", "tap your network"));
  }
}
static void wifi_rescan_cb(lv_event_t *e) { (void)e; wifi_populate(); }

static void ui_wifi() {
  lv_obj_t *scr = lv_screen_active();
  bool canBack = !g_onboarding && g_hasToken;
  thead(scr, TRS("configura wifi", "configure wifi"), canBack ? (g_usage.ok ? ST_MAIN : ST_SETTINGS) : -1);
  tbtn(scr, canBack ? 278 : 375, 5, 92, 32, TRS(U_REFRESH " cerca", U_REFRESH " scan"), F14, C_ACCENT, C_BORDER, wifi_rescan_cb, NULL);

  wifi_status = mklabel(scr, "...", F12, C_MUTED);
  lv_obj_set_pos(wifi_status, 13, 50);

  wifi_list = tlist(scr, 13, 72, 454, 244);

  wifi_ta = lv_textarea_create(scr);
  lv_textarea_set_one_line(wifi_ta, true);
  lv_textarea_set_password_mode(wifi_ta, true);
  lv_textarea_set_placeholder_text(wifi_ta, TRS("password del wifi", "wifi password"));
  lv_obj_set_size(wifi_ta, 456, 40);
  lv_obj_set_pos(wifi_ta, 12, 72);
  style_ta(wifi_ta);
  lv_obj_add_flag(wifi_ta, LV_OBJ_FLAG_HIDDEN);

  wifi_kb = lv_keyboard_create(scr);
  style_kb(wifi_kb);
  lv_obj_add_flag(wifi_kb, LV_OBJ_FLAG_HIDDEN);
  lv_obj_add_event_cb(wifi_kb, wifi_kb_cb, LV_EVENT_ALL, NULL);

  wifi_populate();
}

// ============================================================
// WebServer: token (onboarding) + pagina /models (dashboard)
// ============================================================
static WebServer *g_web = nullptr;
static volatile bool g_tokenGot = false;
static lv_obj_t *g_tokMsg = nullptr;            // stato sullo schermo del dispositivo

static void stop_web() { if (g_web) { g_web->stop(); delete g_web; g_web = nullptr; } }

static bool g_mdnsUp = false;
static void ensure_mdns() {
  if (g_mdnsUp || !g_wifi.isConnected()) return;
  if (MDNS.begin("ritmo-code")) {
    MDNS.addService("http", "tcp", 80);
    g_mdnsUp = true;
    Serial.println("[MDNS] ritmo-code.local");
  }
}

static void anim_opa_cb(void *o, int32_t v) { lv_obj_set_style_opa((lv_obj_t *)o, (lv_opa_t)v, 0); }

// Clawd ufficiale (pixel-art) con "respiro" — sostituisce il vecchio sole a raggi.
static lv_obj_t *build_claude_mark(lv_obj_t *parent) {
  lv_obj_t *img = lv_image_create(parent);
  lv_image_set_src(img, &img_clawd_big);
  lv_anim_t a; lv_anim_init(&a);
  lv_anim_set_var(&a, img);
  lv_anim_set_exec_cb(&a, anim_opa_cb);
  lv_anim_set_values(&a, 140, 255);
  lv_anim_set_duration(&a, 900);
  lv_anim_set_playback_duration(&a, 900);
  lv_anim_set_repeat_count(&a, LV_ANIM_REPEAT_INFINITE);
  lv_anim_start(&a);
  return img;
}

// ---- pagine HTML ----
#define WEB_CSS \
  ":root{--bg:#0F0F12;--card:#1A1A20;--bd:#30303A;--tx:#F2F0EC;--mut:#8C8C98;--cor:#D97757}" \
  "*{box-sizing:border-box}" \
  "body{margin:0;background:var(--bg);color:var(--tx);font-family:-apple-system,Segoe UI,Roboto,sans-serif;" \
  "display:flex;min-height:100vh;align-items:center;justify-content:center}" \
  ".card{background:var(--card);border:1px solid var(--bd);border-radius:16px;padding:26px;max-width:520px;width:92%}" \
  "h1{font-size:19px;margin:0 0 6px;display:flex;align-items:center;gap:10px}" \
  "p{color:var(--mut);font-size:14px;line-height:1.5;margin:6px 0 14px}" \
  "textarea{width:100%;background:var(--bg);color:var(--tx);border:1px solid var(--bd);border-radius:10px;" \
  "padding:12px;font-family:ui-monospace,monospace;font-size:13px;min-height:96px;resize:vertical}" \
  "input{width:100%;background:var(--bg);color:var(--tx);border:1px solid var(--bd);border-radius:10px;" \
  "padding:12px;font-size:14px;margin-bottom:10px}" \
  "button{margin-top:14px;width:100%;background:var(--cor);color:#1A1A20;border:0;border-radius:10px;" \
  "padding:14px;font-size:16px;font-weight:700;cursor:pointer}" \
  ".spark{width:26px;height:26px;flex:0 0 auto}code,a{color:var(--cor)}"

#define WEB_SPARK \
  "<svg class=spark viewBox='0 0 100 100'><g stroke='#D97757' stroke-width='12' stroke-linecap='round'>" \
  "<line x1=50 y1=9 x2=50 y2=91/><line x1=9 y1=50 x2=91 y2=50/>" \
  "<line x1=21 y1=21 x2=79 y2=79/><line x1=79 y1=21 x2=21 y2=79/>" \
  "<line x1=34 y1=11 x2=66 y2=89/><line x1=66 y1=11 x2=34 y2=89/></g></svg>"

static String web_form() {
  String h = F("<!doctype html><html lang=it><head><meta charset=utf-8>"
               "<meta name=viewport content='width=device-width,initial-scale=1'>"
               "<title>Ritmo Code</title><style>" WEB_CSS "</style></head><body><div class=card>"
               "<h1>" WEB_SPARK " Ritmo Code</h1>"
               "<p>Incolla il tuo token OAuth di Claude (<code>sk-ant-oat01-...</code>) e tocca <b>Salva</b>. "
               "Il dispositivo <b>verificherà</b> il token e chiederà un PIN sullo schermo.</p>"
               "<form method=POST action='/token'>"
               "<input name=label maxlength=16 placeholder='etichetta account (es.: Personale, Lavoro)' autocomplete=off>"
               "<textarea name=token placeholder='sk-ant-oat01-...' autocomplete=off autofocus></textarea>"
               "<button type=submit>Salva e verifica</button></form></div></body></html>");
  return h;
}
static String web_result(bool ok, const String &msg) {
  String h = F("<!doctype html><html lang=it><head><meta charset=utf-8>"
               "<meta name=viewport content='width=device-width,initial-scale=1'>"
               "<title>Ritmo Code</title><style>" WEB_CSS "</style></head><body><div class=card>");
  if (ok) {
    h += F("<h1>" WEB_SPARK " Token verificato</h1>"
           "<p>Token accettato dalla API. Ora <b>imposta un PIN di 4 cifre</b> sullo schermo del dispositivo per completare. "
           "Puoi chiudere questa pagina.</p>");
  } else {
    h += F("<h1>" WEB_SPARK " Token rifiutato</h1><p>");
    h += msg;
    h += F("</p><p><a href='/'>Torna indietro e riprova</a></p>");
  }
  h += F("</div></body></html>");
  return h;
}

static void handleRoot()     { g_web->send(200, "text/html; charset=utf-8", web_form()); }
static void handleNotFound() { g_web->sendHeader("Location", "/"); g_web->send(302, "text/plain", ""); }

static void handleTokenPost() {
  String lb = g_web->arg("label");
  lb.trim();
  strlcpy(g_pendingLabel, lb.c_str(), sizeof(g_pendingLabel));
  String t = g_web->arg("token");
  t.trim();
  if (t.length() < 8) {
    if (g_tokMsg) lv_label_set_text(g_tokMsg, TRS("token vuoto", "empty token"));
    g_web->send(200, "text/html; charset=utf-8", web_result(false, "Token vuoto o troppo corto."));
    return;
  }
  if (g_netBusy) {                            // un aggiornamento e' ancora in corso
    g_web->send(200, "text/html; charset=utf-8",
                web_result(false, "Il dispositivo sta finendo un aggiornamento: riprova tra qualche secondo."));
    return;
  }
  // feedback sul dispositivo prima della chiamata bloccante
  if (g_tokMsg) { lv_label_set_text(g_tokMsg, TRS("verifica del token...", "validating token...")); lv_refr_now(NULL); }

  UsageData tmp = {};
  bool ok = fetchUsage(t.c_str(), tmp);
  if (ok) {
    strlcpy(g_pendingToken, t.c_str(), sizeof(g_pendingToken));
    g_usage = tmp;                              // abbiamo gia' i dati per il dashboard
    g_pinConfirming = false; g_pinFirst[0] = 0; g_pinEntry[0] = 0;
    g_tokenGot = true;                          // loop -> ST_SETUP_PIN
    if (g_tokMsg) lv_label_set_text(g_tokMsg, TRS("token OK! imposta il PIN", "token OK! set the PIN"));
    g_web->send(200, "text/html; charset=utf-8", web_result(true, ""));
  } else {
    String m = String("La API ha rifiutato il token (") + tmp.error + "). Controllalo e incollalo di nuovo.";
    if (g_tokMsg) lv_label_set_text(g_tokMsg, TRS("token rifiutato, riprova", "token rejected, try again"));
    g_web->send(200, "text/html; charset=utf-8", web_result(false, m));
  }
}

// ---- / : pagina di stato (stesso tema Terminale del display) ----
// Legge solo /api/status (memoria del dispositivo): nessuna richiesta ad Anthropic, token mai esposto.
// (HTML in status_page.h: il preprocessore Arduino non gestisce le raw string nel .ino)
static void handleInfo() { g_web->send_P(200, "text/html; charset=utf-8", STATUS_PAGE); }

static bool model_up(int i);
static bool night_paused();
static void json_str(String &o, const char *s) {
  o += '"';
  for (; *s; s++) {
    if (*s == '"' || *s == '\\') o += '\\';
    if ((uint8_t)*s >= 0x20) o += *s;
  }
  o += '"';
}
static int model_mood(int i);
static void heat_mode_data(int mode, float out[24]);
// Dati del PC in JSON (pannello web): stessi valori della pagina pc, con i sensori.
// hist = true aggiunge i campioni dei grafici (endpoint /api/pc, letto spesso dalla pagina pc).
static void pc_json(String &o, bool hist) {
  char b[200];
  bool ok = g_pc.ok && g_pcAtMs && millis() - g_pcAtMs <= pc_stale_ms();
  snprintf(b, sizeof(b), "{\"ok\":%s,\"age\":%lu,\"int\":%u,\"kwh\":%.3f,\"host\":", ok ? "true" : "false",
           (unsigned long)(g_pcAtMs ? millis() - g_pcAtMs : 0), (unsigned)PC_INT_S[g_pcIntIdx], g_kwhPrice);
  o += b;
  json_str(o, g_pcHost);
  o += ",\"cpu_name\":"; json_str(o, g_pc.cpuName);
  o += ",\"gpu_name\":"; json_str(o, g_pc.gpuName);
  snprintf(b, sizeof(b), ",\"cpu\":%.1f,\"cpu_t\":%.1f,\"cpu_mhz\":%.0f,\"cpu_w\":%.1f,\"core_max\":%.0f,\"volt\":%.3f,",
           g_pc.cpu, g_pc.cpuTemp, g_pc.cpuMhz, g_pc.cpuPower, g_pc.cpuCoreMax, g_pc.cpuVolt);
  o += b;
  snprintf(b, sizeof(b), "\"gpu\":%.1f,\"gpu_t\":%.1f,\"gpu_w\":%.1f,\"gpu_hot\":%.1f,\"gpu_mem_t\":%.1f,\"gpu_mhz\":%.0f,\"gpu_mem_load\":%.0f,",
           g_pc.gpu, g_pc.gpuTemp, g_pc.gpuPower, g_pc.gpuHotspot, g_pc.gpuMemTemp, g_pc.gpuClockMhz, g_pc.gpuMemLoad);
  o += b;
  snprintf(b, sizeof(b), "\"ram\":%.1f,\"ram_used_gb\":%.2f,\"ram_total_gb\":%.2f,\"vram_used_gb\":%.2f,\"vram_total_gb\":%.2f,\"disk\":%.0f,",
           g_pc.ram, g_pc.ramUsedMb / 1024.0f, g_pc.ramTotalMb / 1024.0f, g_pc.vramUsedMb / 1024.0f, g_pc.vramTotalMb / 1024.0f, g_pc.disk);
  o += b;
  snprintf(b, sizeof(b), "\"net_down\":%.0f,\"net_up\":%.0f,\"disk_r\":%.0f,\"disk_w\":%.0f,\"uptime\":%u,\"claude\":%d,\"disks\":[",
           g_pc.netDown, g_pc.netUp, g_pc.diskRead, g_pc.diskWrite, (unsigned)g_pc.uptime, g_pc.claude);
  o += b;
  for (int d = 0; d < g_pc.diskN; d++) {
    snprintf(b, sizeof(b), "%s[\"%c\",%.1f,%.1f,%.1f]", d ? "," : "", g_pc.disks[d].letter, g_pc.disks[d].used,
             g_pc.disks[d].freeGb, g_pc.disks[d].totalGb);
    o += b;
  }
  o += "],\"fans\":[";
  for (int i = 0; i < g_pc.fanN; i++) {
    o += i ? ",[" : "["; json_str(o, g_pc.fans[i].name);
    snprintf(b, sizeof(b), ",%d]", g_pc.fans[i].rpm); o += b;
  }
  o += "],\"board\":[";
  for (int i = 0; i < g_pc.boardN; i++) {
    o += i ? ",[" : "["; json_str(o, g_pc.board[i].name);
    snprintf(b, sizeof(b), ",%.1f]", g_pc.board[i].value); o += b;
  }
  o += "],\"ram_t\":[";
  for (int i = 0; i < g_pc.ramTempN; i++) { snprintf(b, sizeof(b), "%s%.1f", i ? "," : "", g_pc.ramTemps[i]); o += b; }
  o += "],\"drives\":[";
  for (int i = 0; i < g_pc.driveN; i++) {
    o += i ? ",[" : "["; json_str(o, g_pc.drives[i].name);
    snprintf(b, sizeof(b), ",%.1f,%.1f]", g_pc.drives[i].temp, g_pc.drives[i].life); o += b;
  }
  o += "]";
  if (hist) {
    o += ",\"hist\":[";
    for (int k = 0; k < 3; k++) {
      o += k ? ",[" : "[";
      for (int i = 0; i < g_pcHistN; i++) { snprintf(b, sizeof(b), "%s%u", i ? "," : "", g_pcHist[k][i]); o += b; }
      o += "]";
    }
    o += "]";
  }
  o += "}";
}
static void handleApiPc() {
  String o;
  o.reserve(4000);
  pc_json(o, true);
  g_web->sendHeader("Cache-Control", "no-store");
  g_web->send(200, "application/json", o);
}
// motivo dell'ultimo riavvio (per capire un riavvio inatteso senza collegare l'USB)
static const char *reset_reason_str() {
  switch (esp_reset_reason()) {
    case ESP_RST_POWERON:   return "accensione";
    case ESP_RST_SW:        return "software";
    case ESP_RST_PANIC:     return "errore (panic)";
    case ESP_RST_INT_WDT:   return "watchdog interrupt";
    case ESP_RST_TASK_WDT:  return "task watchdog";
    case ESP_RST_WDT:       return "watchdog";
    case ESP_RST_BROWNOUT:  return "calo di tensione";
    case ESP_RST_DEEPSLEEP: return "risveglio";
    case ESP_RST_USB:       return "usb";
    default:                return "altro";
  }
}
static int h5_forecast(uint32_t *eta, float *endPct);
static void handleApiStatus() {
  String o;
  o.reserve(9000);
  time_t now = time(nullptr);
  char b[160];
  uint32_t updated = (g_lastOkMs && now > 1000000000L) ? (uint32_t)(now - (millis() - g_lastOkMs) / 1000) : 0;
  o += "{\"reset\":\""; o += reset_reason_str(); o += "\",\"uptime\":"; o += (unsigned long)(millis() / 1000); o += ",";
  // diagnostica: RAM interna in KB [libera, blocco piu' grande, minima dall'avvio] e ultimo errore di rete
  snprintf(b, sizeof(b), "\"heap\":[%u,%u,%u],\"fails\":%d,\"err_at\":%u,\"err\":",
           (unsigned)(heap_caps_get_free_size(MALLOC_CAP_INTERNAL) / 1024),
           (unsigned)(heap_caps_get_largest_free_block(MALLOC_CAP_INTERNAL) / 1024),
           (unsigned)(heap_caps_get_minimum_free_size(MALLOC_CAP_INTERNAL) / 1024), g_failN, (unsigned)g_lastErrAt);
  o += b; json_str(o, g_lastErr); o += ',';
  snprintf(b, sizeof(b), "\"fw\":\"" FW_VERSION "\",\"now\":%ld,\"ok\":%s,\"h5\":%.1f,\"d7\":%.1f,\"h5_reset\":%u,\"d7_reset\":%u,",
           (long)now, g_usage.ok ? "true" : "false", g_usage.h5, g_usage.d7,
           (unsigned)g_usage.h5ResetEpoch, (unsigned)g_usage.d7ResetEpoch);
  o += b;
  snprintf(b, sizeof(b), "\"updated\":%u,\"refreshing\":%s,\"night\":%s,\"paused\":%s,\"status\":",
           (unsigned)updated, g_refreshing ? "true" : "false", night_paused() ? "true" : "false", g_userPause ? "true" : "false");
  o += b;
  json_str(o, g_usage.statusOverall);
  o += ",\"account\":";
  json_str(o, g_accts.label[g_accts.active]);
  o += ",\"models\":[";
  for (int i = 0; i < NMODELS; i++) {
    if (i) o += ',';
    o += "{\"name\":"; json_str(o, g_models[i].name);
    o += ",\"id\":";   json_str(o, g_models[i].id);
    long age = g_models[i].atMs ? (long)((millis() - g_models[i].atMs) / 1000) : -1;
    snprintf(b, sizeof(b), ",\"code\":%d,\"ms\":%u,\"up\":%s,\"mood\":%d,\"age\":%ld,\"msg\":",
             g_models[i].pr.code, (unsigned)g_models[i].pr.ms, model_up(i) ? "true" : "false", model_mood(i), age);
    o += b;
    json_str(o, g_models[i].pr.msg);
    o += '}';
  }
  o += "],\"hist\":[";
  bool first = true;
  for (int i = 0; i < g_histN; i++) {
    const Sample &s = g_hist[(g_histHead - g_histN + i + HIST_MAX) % HIST_MAX];
    if (!s.t) continue;
    snprintf(b, sizeof(b), "%s[%u,%u,%u]", first ? "" : ",", (unsigned)s.t, s.h5, s.d7);
    o += b; first = false;
  }
  // ritmo orario per periodo (oggi, 7g, 30g, tutto): come la pagina ritmo del display
  o += "],\"heat\":[";
  for (int m = 0; m < 4; m++) {
    float d[24];
    heat_mode_data(m, d);
    o += m ? ",[" : "[";
    for (int h = 0; h < 24; h++) { snprintf(b, sizeof(b), "%s%.1f", h ? "," : "", d[h]); o += b; }
    o += "]";
  }
  o += "],\"weeks\":[";
  for (int i = 0; i < g_weekN; i++) {
    snprintf(b, sizeof(b), "%s[%u,%u]", i ? "," : "", (unsigned)g_weeks[i].reset, g_weeks[i].peak);
    o += b;
  }
  snprintf(b, sizeof(b), "],\"pause_until\":%u,\"heat_mode\":%d,", (unsigned)g_pauseUntil, g_heatMode);
  o += b;
  {                                                // previsione 5h: [tipo, fine, % al reset] (tipi di h5_forecast)
    uint32_t eta = 0; float endPct = 0;
    int fc = h5_forecast(&eta, &endPct);
    snprintf(b, sizeof(b), "\"fc5\":[%d,%u,%.0f],", fc, (unsigned)eta, endPct);
    o += b;
  }
  {                                                // progetti dal PC Monitor (pagina ritmo)
    bool pcOk = g_pc.ok && g_pcAtMs && millis() - g_pcAtMs <= pc_stale_ms();
    o += "\"cc_pl\":[";
    for (int i = 0; i < 4; i++) { if (i) o += ','; json_str(o, pcOk ? g_pc.ccPl[i] : ""); }
    o += "],\"cc_pa\":"; json_str(o, pcOk ? g_pc.ccPa : ""); o += ',';
  }
  {                                                // timer e pomodoro (per il menu dell'icona sul PC)
    char tl[40] = "";
    if (g_tmMode) tm_label(tl, sizeof(tl));
    snprintf(b, sizeof(b), "\"timer\":{\"mode\":%d,\"left\":%u,\"label\":\"%s\"},", g_tmMode,
             (unsigned)(g_tmMode ? tm_left_s() : 0), tl);
    o += b;
  }
  snprintf(b, sizeof(b), "\"wx\":{\"ok\":%s,\"city\":", g_wx.ok ? "true" : "false");
  o += b;
  json_str(o, g_wxCity);
  snprintf(b, sizeof(b), ",\"temp\":%.1f,\"code\":%d,\"day\":%s,\"tmax\":%.1f,\"tmin\":%.1f,\"tmax2\":%.1f,\"tmin2\":%.1f,\"code2\":%d,",
           g_wx.temp, g_wx.code, g_wx.isDay ? "true" : "false", g_wx.tmax, g_wx.tmin, g_wx.tmax2, g_wx.tmin2, g_wx.code2);
  o += b;
  snprintf(b, sizeof(b), "\"sunrise\":\"%s\",\"sunset\":\"%s\",\"rain_h0\":%d,\"rain\":[", g_wx.sunrise, g_wx.sunset, g_wx.rainHour0);
  o += b;
  for (int i = 0; i < 12; i++) { snprintf(b, sizeof(b), "%s%u", i ? "," : "", g_wx.rain[i]); o += b; }
  o += "]},\"pc\":";
  pc_json(o, false);
  o += "}";
  g_web->sendHeader("Cache-Control", "no-store");
  g_web->send(200, "application/json", o);
}
// ---- /models: ID dei modelli sondati, modificabili dal browser ----
static String models_page(const String &msg, bool ok) {
  String h = F("<!doctype html><html lang=it><head><meta charset=utf-8>"
               "<meta name=viewport content='width=device-width,initial-scale=1'>"
               "<title>Modelli - Ritmo Code</title><style>" WEB_CSS
               "label{display:block;font-size:13px;color:var(--mut);margin:12px 0 4px}"
               "input{margin-bottom:0;font-family:ui-monospace,monospace}"
               ".msg{padding:10px 12px;border-radius:10px;margin:0 0 12px;font-size:14px}"
               ".ok{background:#4ADE8022;color:#4ADE80}.err{background:#F8717122;color:#F87171}"
               "</style></head><body><div class=card>"
               "<h1>" WEB_SPARK " Modelli sondati</h1>"
               "<p>Il dispositivo controlla un modello per ciclo con l'ID indicato qui. "
               "Se Anthropic cambia i nomi, aggiornali copiandoli dalla "
               "<a href='https://docs.anthropic.com/en/docs/about-claude/models' target=_blank>documentazione</a>. "
               "Lascia vuoto per tornare al predefinito.</p>");
  if (msg.length()) {
    h += ok ? "<div class='msg ok'>" : "<div class='msg err'>";
    h += msg;
    h += "</div>";
  }
  h += F("<form method=POST action='/models'>");
  for (int i = 0; i < NMODELS; i++) {
    h += "<label for=m"; h += i; h += ">"; h += g_models[i].name; h += "</label>";
    h += "<input id=m"; h += i; h += " name=m"; h += i;
    h += " maxlength=47 autocomplete=off autocapitalize=off spellcheck=false value='";
    h += g_models[i].id;                      // gia' validato: solo a-z 0-9 . - _
    h += "' placeholder='"; h += g_models[i].defId; h += "'>";
  }
  h += F("<label for=pin>PIN del dispositivo</label>"
         "<input id=pin name=pin type=password inputmode=numeric maxlength=4 autocomplete=off>"
         "<button type=submit>Salva</button></form></div></body></html>");
  return h;
}
static void handleModelsGet() { g_web->send(200, "text/html; charset=utf-8", models_page("", true)); }
// PIN richiesto per modificare dal browser: 5 errori bloccano per 5 minuti
static int g_webPinBad = 0;
static uint32_t g_webPinLockMs = 0;
static bool web_pin_ok(String &err) {
  if (g_webPinLockMs && millis() - g_webPinLockMs < 5UL * 60UL * 1000UL) {
    err = "Troppi PIN errati: riprova tra qualche minuto."; return false;
  }
  g_webPinLockMs = 0;
  if (!g_sessionPin[0]) { err = "Sblocca prima il dispositivo con il PIN."; return false; }
  if (g_web->arg("pin") != g_sessionPin) {
    if (++g_webPinBad >= 5) { g_webPinBad = 0; g_webPinLockMs = millis(); }
    Serial.println("[WEB] PIN errato su /models");
    err = "PIN errato: nessuna modifica salvata."; return false;
  }
  g_webPinBad = 0;
  return true;
}
static void handleModelsPost() {
  String perr;
  if (!web_pin_ok(perr)) { g_web->send(403, "text/html; charset=utf-8", models_page(perr, false)); return; }
  String bad;
  for (int i = 0; i < NMODELS; i++) {
    char arg[4]; snprintf(arg, sizeof(arg), "m%d", i);
    if (!g_web->hasArg(arg)) continue;
    if (!model_set_id(i, g_web->arg(arg).c_str())) {
      if (bad.length()) bad += ", ";
      bad += g_models[i].name;
    }
  }
  if (g_state == ST_MAIN || g_state == ST_MODELS) request_state(g_state);   // ridisegna mascotte/lista
  if (bad.length())
    g_web->send(200, "text/html; charset=utf-8",
                models_page("ID non valido per " + bad + ": usa solo a-z, 0-9, punto, trattino e underscore (3-47 caratteri).", false));
  else
    g_web->send(200, "text/html; charset=utf-8",
                models_page("Salvato. Il controllo usa i nuovi ID dal prossimo giro, senza richieste extra.", true));
}

// ---- /update: firmware via Wi-Fi ----
// Attivo solo con la schermata "aggiorna firmware" aperta sul dispositivo: serve il codice
// di 6 cifre mostrato sullo schermo (presenza fisica). 5 codici sbagliati chiudono la sessione.
#define OTA_WINDOW_MS (5UL * 60UL * 1000UL)
static char g_otaCode[8] = {0};
static uint32_t g_otaStartMs = 0;
static int g_otaBad = 0;
static bool g_otaBusy = false, g_otaAuth = false, g_otaDone = false;
static uint32_t g_otaRebootAt = 0;
static size_t g_otaBytes = 0;
static String g_otaErr;
static lv_obj_t *g_otaStat = nullptr, *g_otaBar = nullptr, *g_otaTime = nullptr;

static bool ota_open() { return g_state == ST_OTA && g_otaCode[0]; }
static void ota_status(const char *txt, uint32_t col) {
  if (g_otaStat) { lv_label_set_text(g_otaStat, txt); lv_obj_set_style_text_color(g_otaStat, lv_color_hex(col), 0); }
}
static void handleUpdateGet() {
  String h = F("<!doctype html><html lang=it><head><meta charset=utf-8>"
               "<meta name=viewport content='width=device-width,initial-scale=1'>"
               "<title>Aggiorna - Ritmo Code</title><style>" WEB_CSS
               "label{display:block;font-size:13px;color:var(--mut);margin:12px 0 4px}"
               "input[type=file]{padding:10px}"
               "progress{width:100%;height:10px;margin-top:14px;accent-color:var(--cor)}"
               "#msg{margin-top:12px;font-size:14px;color:var(--mut)}"
               "</style></head><body><div class=card>"
               "<h1>" WEB_SPARK " Aggiorna firmware</h1>");
  if (!ota_open()) {
    h += F("<p>Sul dispositivo apri <b>Impostazioni &rarr; aggiorna firmware</b>: comparira' un codice "
           "di 6 cifre valido 5 minuti. Poi ricarica questa pagina.</p></div></body></html>");
    g_web->send(200, "text/html; charset=utf-8", h);
    return;
  }
  h += F("<p>Firmware attuale v" FW_VERSION ". Scegli il file <code>ritmo-code-x.y.bin</code> della release "
         "(o <code>ritmo_code.ino.bin</code> da <code>firmware/ritmo_code/build/...</code> se lo compili tu) "
         "e inserisci il codice mostrato sullo schermo.</p>"
         "<label for=code>Codice</label><input id=code inputmode=numeric maxlength=6 autocomplete=off>"
         "<label for=bin>File firmware (.bin)</label><input id=bin type=file accept='.bin'>"
         "<button id=go>Carica</button><progress id=pr max=100 value=0 hidden></progress><div id=msg></div>"
         "<script>"
         "go.onclick=function(){var f=bin.files[0];if(!f){msg.textContent='Scegli un file .bin';return}"
         "var fd=new FormData();fd.append('firmware',f);var x=new XMLHttpRequest();"
         "x.open('POST','/update?code='+encodeURIComponent(code.value));pr.hidden=false;go.disabled=true;"
         "x.upload.onprogress=function(e){if(e.lengthComputable)pr.value=e.loaded*100/e.total};"
         "x.onload=function(){msg.textContent=x.responseText;go.disabled=false};"
         "x.onerror=function(){msg.textContent='Connessione interrotta';go.disabled=false};x.send(fd)}"
         "</script></div></body></html>");
  g_web->send(200, "text/html; charset=utf-8", h);
}
static void handleUpdateUpload() {
  HTTPUpload &up = g_web->upload();
  if (up.status == UPLOAD_FILE_START) {
    g_otaAuth = false; g_otaErr = ""; g_otaBytes = 0;
    if (!ota_open())                                   { g_otaErr = "Schermata di aggiornamento chiusa sul dispositivo"; return; }
    if (g_web->arg("code") != g_otaCode) {
      g_otaErr = "Codice errato";
      if (++g_otaBad >= 5) { g_otaCode[0] = 0; g_otaErr = "Troppi tentativi: riapri la schermata sul dispositivo"; }
      return;
    }
    if (!Update.begin(UPDATE_SIZE_UNKNOWN, U_FLASH))   { g_otaErr = String("Avvio fallito: ") + Update.errorString(); return; }
    g_otaAuth = true; g_otaBusy = true;
    Serial.printf("[OTA] ricezione %s\n", up.filename.c_str());
    ota_status(TRS("ricezione in corso...", "receiving..."), C_WARN);
    lv_timer_handler();
  } else if (up.status == UPLOAD_FILE_WRITE) {
    if (!g_otaAuth) return;
    if (Update.write(up.buf, up.currentSize) != up.currentSize) {
      g_otaErr = String("Scrittura fallita: ") + Update.errorString();
      Update.abort(); g_otaAuth = false; g_otaBusy = false;
      return;
    }
    size_t before = g_otaBytes;
    g_otaBytes += up.currentSize;
    if (g_otaBytes / 65536 != before / 65536) {        // ~ogni 64 KB: aggiorna lo schermo
      char s[40]; snprintf(s, sizeof(s), TRS("ricevuti %u KB", "received %u KB"), (unsigned)(g_otaBytes / 1024));
      ota_status(s, C_WARN);
      // dimensione finale ignota: stima sul firmware attuale (le versioni hanno taglie simili)
      uint32_t est = ESP.getSketchSize();
      if (g_otaBar && est) lv_bar_set_value(g_otaBar, (int)min<uint64_t>(99, (uint64_t)g_otaBytes * 100 / est), LV_ANIM_OFF);
      lv_timer_handler();
    }
  } else if (up.status == UPLOAD_FILE_END) {
    if (!g_otaAuth) return;
    if (Update.end(true)) {
      g_otaDone = true;
      Serial.printf("[OTA] ok, %u byte\n", (unsigned)up.totalSize);
    } else {
      g_otaErr = String("Verifica fallita: ") + Update.errorString();
    }
    g_otaAuth = false; g_otaBusy = false;
  } else if (up.status == UPLOAD_FILE_ABORTED) {
    if (g_otaAuth) Update.abort();
    g_otaAuth = false; g_otaBusy = false;
    g_otaErr = "Caricamento interrotto";
  }
}
static void handleUpdatePost() {
  if (g_otaDone) {
    g_web->send(200, "text/plain; charset=utf-8", "Aggiornamento completato: il dispositivo si riavvia.");
    ota_status(TRS("completato " U_MIDDOT " riavvio...", "done " U_MIDDOT " rebooting..."), C_OK);
    if (g_otaBar) lv_bar_set_value(g_otaBar, 100, LV_ANIM_OFF);
    g_otaRebootAt = millis() + 1500;
    return;
  }
  if (!g_otaErr.length()) g_otaErr = "Nessun file ricevuto";
  Serial.printf("[OTA] rifiutato: %s\n", g_otaErr.c_str());
  ota_status(g_otaErr.c_str(), C_BAD);
  g_web->send(g_otaErr == "Codice errato" ? 403 : 400, "text/plain; charset=utf-8", g_otaErr);
}

// ---- /home: citta' del meteo e indirizzo del PC (ricerca citta' fatta dal browser) ----
static String home_page(const String &msg, bool ok) {
  String h = F("<!doctype html><html lang=it><head><meta charset=utf-8>"
               "<meta name=viewport content='width=device-width,initial-scale=1'>"
               "<title>Home - Ritmo Code</title><style>" WEB_CSS
               "label{display:block;font-size:13px;color:var(--mut);margin:12px 0 4px}"
               "input,select{margin-bottom:0}select{width:100%;background:var(--bg);color:var(--tx);border:1px solid var(--bd);border-radius:10px;padding:12px}"
               ".msg{padding:10px 12px;border-radius:10px;margin:0 0 12px;font-size:14px}"
               ".ok{background:#4ADE8022;color:#4ADE80}.err{background:#F8717122;color:#F87171}"
               ".row{display:flex;gap:8px}.row button{margin-top:0;width:auto;padding:0 16px}"
               "</style></head><body><div class=card>"
               "<h1>" WEB_SPARK " Pagina home</h1>"
               "<p>Le impostazioni che stanno sul dispositivo: meteo, PC, energia e calendario. "
               "Avvisi, schermo e suoni sono in <i>Impostazioni</i> sul dispositivo.</p>"
               "<style>h2{font-size:13px;color:var(--mut);text-transform:lowercase;margin:22px 0 0;"
               "border-top:1px solid var(--bd);padding-top:14px;font-weight:500}h2:first-of-type{border:0;margin-top:8px}</style>");
  if (msg.length()) { h += ok ? "<div class='msg ok'>" : "<div class='msg err'>"; h += msg; h += "</div>"; }
  char num[24];
  h += F("<form method=POST action='/home' id=f><h2 id=citta>home e meteo</h2><label for=q>Citta'</label><div class=row>"
         "<input id=q autocomplete=off value='");
  h += g_wxCity;
  h += F("'><button type=button id=s>Cerca</button></div><select id=r hidden></select>"
         "<input type=hidden name=city id=city value='");
  h += g_wxCity;
  h += F("'><input type=hidden name=lat id=lat value='");
  snprintf(num, sizeof(num), "%.4f", g_wxLat); h += num;
  h += F("'><input type=hidden name=lon id=lon value='");
  snprintf(num, sizeof(num), "%.4f", g_wxLon); h += num;
  h += F("'><h2 id=pc>rete e pc</h2><label for=pcf>Indirizzo del PC (ip:porta, vuoto per nasconderlo)</label>"
         "<input id=pcf name=pc maxlength=47 autocomplete=off placeholder='192.168.1.10:8080' value='");
  h += g_pcHost;
  h += F("'><label for=kwhf>Prezzo dell'energia (euro per kWh, per il costo del PC)</label>"
         "<input id=kwhf name=kwh inputmode=decimal maxlength=6 autocomplete=off value='");
  snprintf(num, sizeof(num), "%.3f", g_kwhPrice); h += num;
  h += F("'><h2 id=cal>calendario</h2><label for=ical>Indirizzo segreto in formato iCal (Google Calendar dal browser: Impostazioni &rarr; "
         "il tuo calendario &rarr; Integra il calendario &rarr; <b>Indirizzo segreto in formato iCal</b>, non quello pubblico)</label>"
         "<input id=ical name=ical maxlength=250 autocomplete=off placeholder='");
  h += g_ical[0] ? F("impostato: lascia vuoto per non cambiarlo") : F("https://calendar.google.com/calendar/ical/.../basic.ics");
  h += F("'>");
  if (g_ical[0]) h += F("<label><input type=checkbox name=icaldel value=1 style='width:auto;margin-right:6px'>rimuovi il calendario</label>");
  h += F("<p style='font-size:12px;color:var(--mut)'>Il link lo legge solo il PC collegato (Ritmo Code PC Monitor), che scarica gli eventi ogni 5 minuti.</p>");
  h += F("<h2 id=cd>conto alla rovescia</h2><p style='font-size:12px;color:var(--mut)'>Fino a tre date, con nome e giorno/ora. "
         "Svuota il nome per togliere una riga. Sul dispositivo: tendina &rarr; conto.</p><input type=hidden name=cdform value=1>");
  for (int i = 0; i < CD_MAX; i++) {
    char nm[8], dt[24];
    snprintf(nm, sizeof(nm), "%d", i);
    dt[0] = 0;
    if (i < g_cdN) { time_t t = g_cd[i].at; struct tm v; localtime_r(&t, &v);
      snprintf(dt, sizeof(dt), "%04d-%02d-%02dT%02d:%02d", v.tm_year + 1900, v.tm_mon + 1, v.tm_mday, v.tm_hour, v.tm_min); }
    h += F("<div class=row style='margin-top:8px'><input style='flex:1' maxlength=40 autocomplete=off placeholder='nome' name=cdt");
    h += nm; h += F(" value='");
    if (i < g_cdN) for (const char *q = g_cd[i].title; *q; q++) {
      if (*q == '\'') h += F("&#39;"); else if (*q == '&') h += F("&amp;"); else if (*q == '<') h += F("&lt;"); else h += *q;
    }
    h += F("'><input type=datetime-local style='max-width:215px' name=cdd"); h += nm; h += F(" value='"); h += dt; h += F("'></div>");
  }
  h += F("<h2>salva</h2><label for=pin>PIN del dispositivo</label>"
         "<input id=pin name=pin type=password inputmode=numeric maxlength=4 autocomplete=off>"
         "<button type=submit>Salva</button></form><p><a href='/'>&larr; pannello</a></p>"
         "<script>var R=[];s.onclick=function(){fetch('https://geocoding-api.open-meteo.com/v1/search?count=5&language=it&name='+encodeURIComponent(q.value))"
         ".then(function(x){return x.json()}).then(function(j){R=j.results||[];r.hidden=!R.length;"
         "r.innerHTML=R.map(function(c,i){return '<option value='+i+'>'+c.name+(c.admin1?', '+c.admin1:'')+(c.country?' ('+c.country+')':'')+'</option>'}).join('');"
         "if(R.length)pick(0);else alert('Nessuna citta trovata')})};"
         "function pick(i){var c=R[i];city.value=c.name;lat.value=c.latitude.toFixed(4);lon.value=c.longitude.toFixed(4);q.value=c.name}"
         "r.onchange=function(){pick(+r.value)}</script></div></body></html>");
  return h;
}
static void handleHomeGet() { g_web->send(200, "text/html; charset=utf-8", home_page("", true)); }
// l'app Ritmo Code PC Monitor comunica il proprio indirizzo (serve il PIN)
static void handlePcPair() {
  String perr;
  if (!web_pin_ok(perr)) {
    String j = "{\"ok\":false,\"error\":\""; j += perr; j += "\"}";
    g_web->send(403, "application/json", j);
    return;
  }
  String pc = g_web->arg("pc");
  bool ok = pc.length() > 0 && pc.length() < 48;
  for (size_t i = 0; i < pc.length() && ok; i++) {
    char c = pc[i];
    ok = isalnum((unsigned char)c) || c == '.' || c == ':' || c == '-';
  }
  if (!ok) { g_web->send(400, "application/json", "{\"ok\":false,\"error\":\"indirizzo del pc non valido\"}"); return; }
  strlcpy(g_pcHost, pc.c_str(), sizeof(g_pcHost));
  g_prefs.putString("pchost", g_pcHost);
  g_pc.ok = false; g_pcAtMs = 0; g_pcTryMs = 0; g_pcHistN = 0;
  Serial.printf("[PC] collegato dall'app: %s\n", g_pcHost);
  home_redraw();
  g_web->send(200, "application/json", "{\"ok\":true}");
}
// evento degli hook di Claude Code inoltrato da Ritmo Code PC Monitor: solo dal PC collegato
static void handleClaudeEvent() {
  String host = g_pcHost;
  int c = host.indexOf(':');
  if (c >= 0) host.remove(c);
  IPAddress pc;
  if (!g_pcHost[0] || (pc.fromString(host) && g_web->client().remoteIP() != pc)) {
    g_web->send(403, "application/json", "{\"ok\":false}");
    return;
  }
  String ev = g_web->arg("ev"), proj = g_web->arg("proj");
  if (ev != "busy" && ev != "done" && ev != "perm" && ev != "ask") {
    g_web->send(400, "application/json", "{\"ok\":false}");
    return;
  }
  char pj[28]; size_t n = 0;
  for (size_t i = 0; i < proj.length() && n < sizeof(pj) - 1; i++) {
    char ch = proj[i];
    if (isalnum((unsigned char)ch) || ch == '.' || ch == '_' || ch == '-' || ch == ' ') pj[n++] = ch;
  }
  pj[n] = 0;
  if (g_web->hasArg("busy")) { g_ccBusyN = g_web->arg("busy").toInt(); cc_busy_ui(); }
  cc_event(g_web->arg("id").toInt(), ev.c_str(), pj, g_web->hasArg("dur") ? g_web->arg("dur").toInt() : -1, 0);
  g_web->send(204, "text/plain", "");
}
// link iCal per il PC Monitor: solo al PC collegato (il link e' segreto)
static void handleIcalGet() {
  String host = g_pcHost;
  int c = host.indexOf(':');
  if (c >= 0) host.remove(c);
  IPAddress pc;
  if (!g_pcHost[0] || (pc.fromString(host) && g_web->client().remoteIP() != pc)) {
    g_web->send(403, "application/json", "{\"ok\":false}");
    return;
  }
  String j = String("{\"url\":\"") + g_ical + "\"}";
  g_web->send(200, "application/json", j);
}
// timer e pomodoro dal PC (menu dell'icona di Ritmo Code PC Monitor): solo dal PC collegato
static void handleTimerCmd() {
  String host = g_pcHost;
  int c = host.indexOf(':');
  if (c >= 0) host.remove(c);
  IPAddress pc;
  if (!g_pcHost[0] || (pc.fromString(host) && g_web->client().remoteIP() != pc)) {
    g_web->send(403, "application/json", "{\"ok\":false}");
    return;
  }
  String a = g_web->arg("a");
  int opt = -1;
  if (a == "pomo")       opt = constrain(g_web->arg("p").toInt(), 0, 2);
  else if (a == "timer") opt = 100 + constrain(g_web->arg("m").toInt(), 1, 180);
  else if (a == "stop")  opt = 10;
  else if (a == "skip")  opt = 11;
  else if (a == "plus")  opt = 12;
  bool ok = opt >= 0 && tm_action(opt);
  char st[40] = "";
  if (g_tmMode) tm_label(st, sizeof(st));
  String j = String("{\"ok\":") + (ok ? "true" : "false") + ",\"mode\":" + g_tmMode + ",\"label\":\"" + st + "\"}";
  g_web->send(ok ? 200 : 409, "application/json", j);
}
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
void loop() {
  lv_task_handler();
  perf_tick();
  spin_tick();

  // Server web (token durante l'onboarding; /models sul dashboard)
  if (g_web) {
    g_web->handleClient();
    if (g_state == ST_TOKEN && g_tokenGot) {
      g_tokenGot = false;
      if (g_onboarding || !g_sessionPin[0]) request_state(ST_SETUP_PIN);
      else finalize_pending_token();
    }
  }
  ota_tick();
  ota_health_tick();

  if (g_dirty) {
    g_dirty = false;
    render_state();
    g_loadPending = (g_state == ST_LOADING);   // il caricamento parte appena il task e' libero
  }

  // Rete in background: avvio del primo caricamento, risultati pronti, poll/refresh
  if (g_loadPending && g_state == ST_LOADING && net_start(true)) g_loadPending = false;
  if (g_netDone) net_apply();
  // aggiornamento: il task di rete installa appena ha finito il giro in corso
  if (g_updInstallReq && !g_updRunning && !g_netBusy && !g_netDone) {
    g_updRunning = true; g_netBusy = true;
    xTaskNotifyGive(g_netTask);
  }
  if ((g_updState == UPD_INSTALLING || g_updState == UPD_REBOOT) && !g_upd.scrim) upd_overlay();   // dopo un cambio di schermata
  upd_tick();
  if (g_updDone && millis() - g_updCheckStartMs >= 1500) {   // il risultato sostituisce "controllo..." dopo 1,5 s
    g_updDone = false;
    set_hdr_status();
    if (g_state == ST_SETTINGS) request_state(ST_SETTINGS);
  }
  // controllo automatico della nuova versione: 90 s dopo l'avvio, poi una volta al giorno
  if (g_state == ST_MAIN && g_wifi.isConnected() && !g_updCheckReq && g_updState != UPD_INSTALLING &&
      g_updState != UPD_REBOOT && millis() > 90000UL &&
      (!g_updCheckedMs || millis() - g_updCheckedMs > 24UL * 3600UL * 1000UL)) {
    g_updCheckedMs = millis();
    if (g_updState != UPD_AVAILABLE) g_updState = UPD_CHECKING;
    g_updCheckReq = true;
  }
  screen_tick();
  auto_bri_tick(false);
  night_clock_sync();
  tm_tick();
  // home: meteo ogni 30 min (nuovo tentativo dopo 5 min se fallisce), PC ogni 5 s se la home e' visibile
  if (g_calAllDone) {
    g_calAllDone = false;
    if (g_calAllRes >= 0 && g_calAll) {
      memcpy(g_calAll, g_calTmp, sizeof(CalItem) * g_calAllRes);
      g_calAllN = g_calAllRes; g_calAllAtMs = millis();
    }
    if (g_calView) cal_view_build();
  }
  if (g_mcDone) {                                   // copertina arrivata dal task extra
    g_mcDone = false;
    if (g_mcOk && g_mcImg && g_mcGot == g_mcWant) {
      memcpy(g_mcImg, g_mcTmp, MC_N * MC_N * 2);
      g_mcId = g_mcGot; g_mcHave = true;
      lv_image_cache_drop(&g_mcDsc);
      media_view_update(true);
    } else if (g_mcOk) {
      g_mcWant = 0;                                  // il brano e' cambiato nel frattempo: si riprova
    }
  }
  if (g_wxDone) {
    g_wxDone = false;
    if (g_wxRes.ok) { g_wx = g_wxRes; g_wxAtMs = millis(); }
    home_redraw();
    if (g_wxWeek) { wx_week_close(); wx_week_open(nullptr); }
  }
  if (g_pcDone) {
    g_pcDone = false;
    const size_t MOFS = offsetof(PcStats, mediaSt), MLEN = offsetof(PcStats, mediaApp) + sizeof(g_pc.mediaApp) - MOFS;
    if (!g_pcRes.ok) memcpy((uint8_t *)&g_pcRes + MOFS, (uint8_t *)&g_pc + MOFS, MLEN);
    g_pc = g_pcRes;
    if (!g_pc.ok) media_view_update(false);
    if (g_pc.ok) {
      g_pcAtMs = millis();
      if (g_pc.ccId) cc_event(g_pc.ccId, g_pc.ccEv, g_pc.ccProj, g_pc.ccDur, g_pc.ccAge);
      if (g_pc.ccBusy != g_ccBusyN) { g_ccBusyN = g_pc.ccBusy; cc_busy_ui(); }
      media_on_pc();
      if (g_pc.calN >= 0) {
        g_calN = g_pc.calN;
        for (int i = 0; i < g_calN; i++) { g_cal[i].s = g_pc.cal[i].s; g_cal[i].e = g_pc.cal[i].e; strlcpy(g_cal[i].title, g_pc.cal[i].title, sizeof(g_cal[i].title)); }
      }
    }
    if (g_pc.ok) {                                   // il grafico avanza a ogni lettura
      g_pcHistAtMs = millis();
      float v[3] = {g_pc.cpu, g_pc.gpu, g_pc.ram};
      if (g_pcHistN == PC_HIST) { for (int k = 0; k < 3; k++) memmove(g_pcHist[k], g_pcHist[k] + 1, PC_HIST - 1); g_pcHistN--; }
      for (int k = 0; k < 3; k++) g_pcHist[k][g_pcHistN] = (uint8_t)(v[k] < 0 ? 0 : (v[k] > 100 ? 100 : v[k] + 0.5f));
      g_pcHistN++;
    }
    pc_redraw();
    home_redraw();
    sess_redraw();
  }
  if (g_state == ST_MAIN && g_wifi.isConnected() && g_screenMode < 2 && !g_wxReq && !g_wxDone && g_wxLat != 0) {
    bool due = g_wx.ok ? millis() - g_wxAtMs > 30UL * 60UL * 1000UL : (g_wxTryMs == 0 || millis() - g_wxTryMs > 5UL * 60UL * 1000UL);
    if (due) { g_wxTryMs = millis(); g_wxReq = true; }
  }
  if (g_state == ST_MAIN && g_pcHost[0] && g_screenMode < 2 && !g_pcReq && !g_pcDone &&
      (int32_t)(millis() - g_pcTryMs) >= (int32_t)pc_int_ms() - 50) {
    g_pcTryMs = millis();
    strlcpy(g_pcReqHost, g_pcHost, sizeof(g_pcReqHost));
    g_pcReq = true;
  }
  if (g_state == ST_MAIN && !g_netBusy && (g_wantRefresh || !polling_paused()) &&
      (g_wantRefresh || millis() - g_lastPollMs > (uint32_t)g_pollSec * 1000)) {
    if (net_start(false)) g_wantRefresh = false;
  }

  // Aggiornamento continuo: contatori (1s), barra di refresh (250ms), mascotte,
  // slideshow (5s, pausa di 10s dopo qualsiasi tocco)
  if (g_state == ST_MAIN) {
    uint32_t now = millis();
    static uint32_t lastTick = 0, lastBar = 0, lastBob = 0, blinkAt = 0;
    static bool blinkClosed = false;
    // schermo: l'ora si sposta di 2 px ogni 10 min e ogni 30 min si ridisegna tutto (ritenzione dell'immagine)
    static uint32_t lastShift = 0;
    if (g_ui.hmTime && now - lastShift > 600000UL) {
      lastShift = now;
      static int k = 0;
      const int dx[4] = {0, 2, 0, -2}, dy[4] = {0, 1, 2, 1};
      k = (k + 1) % 4;
      lv_obj_set_pos(g_ui.hmTime, 7 + dx[k], 7 + dy[k]);
      if ((k % 2) == 0) lv_obj_invalidate(lv_screen_active());
    }
    if (now - lastTick > 1000) {
      lastTick = now; dash_tick(); home_tick(); if (g_tmMode) set_hdr_status();
      cal_tick();
      tm_restore();
      brk_tick();
      wk_tick();
      cd_tick();
      if (g_mv.scr) media_view_progress();
      if (g_cdv.scr) cd_view_tick();
      home_cd_tick();
      if (g_shadeTm) { char tt[12]; shade_timer_text(tt, sizeof(tt)); label_set(g_shadeTm, tt); }
      if (g_ccBusyN && (!g_pcAtMs || now - g_pcAtMs > pc_stale_ms())) { g_ccBusyN = 0; cc_busy_ui(); }
    }
    static uint32_t lastSpark = 0;
    static int sparkK = 4;
    if (g_ccBusyN > 0 && g_ui.hdrSpark && g_screenMode < 2 && now - lastSpark > 160) {
      lastSpark = now; sparkK = (sparkK + 1) % 10;
      char sp[8]; snprintf(sp, sizeof(sp), "%s ", SPIN[sparkK]);
      label_set(g_ui.hdrSpark, sp);
    }
    if (now - lastBar > 1000 && g_ui.refBar) {       // filo del refresh: al massimo 1 ridisegno/s
      lastBar = now;
      const int W = 275;
      int v;
      if (g_refreshing) v = W;
      else if (polling_paused()) v = 0;
      else {
        uint32_t el = now - g_lastPollMs, per = (uint32_t)g_pollSec * 1000;
        v = el >= per ? 0 : (int)(W - (uint64_t)el * W / per);
      }
      if (v != lv_obj_get_width(g_ui.refBar)) lv_obj_set_width(g_ui.refBar, v);   // solo se cambia
    }
    if (cur_page() == PG_SESS) sess_blink_tick();
    // cursore ▌ della riga di prompt: lampeggia solo sulla pagina Ora
    static uint32_t lastCur = 0;
    if (g_ui.agCursor && cur_page() == PG_ORA && now - lastCur > 700 && now - g_lastTouchMs > 400) {
      lastCur = now;
      if (lv_obj_has_flag(g_ui.agCursor, LV_OBJ_FLAG_HIDDEN)) lv_obj_clear_flag(g_ui.agCursor, LV_OBJ_FLAG_HIDDEN);
      else                                                     lv_obj_add_flag(g_ui.agCursor, LV_OBJ_FLAG_HIDDEN);
    }
    // Le mascotte vivono solo sulla pagina Modelli: animarle altrove (o mentre si
    // scorre) costava ridisegni continui senza che nessuno le vedesse.
    bool mascLive = (cur_page() == PG_MODELS) && (now - g_lastTouchMs > 400) && !g_mo.scrim;
    if (mascLive && now - lastBob > 80) {           // animazione in base all'umore
      lastBob = now;
      float ph = now / 600.0f;
      for (int i = 0; i < g_mascN; i++) {
        if (!g_masc[i].cont) continue;
        if (g_masc[i].mood == 1)                    // ok: ondeggia allegro
          lv_obj_set_y(g_masc[i].cont, g_masc[i].baseY + (int)(2.0f * sinf(ph + i * 0.9f) - 1.0f));
        else if (g_masc[i].mood == 2) {             // limitato: ondeggio corto + sudore
          lv_obj_set_y(g_masc[i].cont, g_masc[i].baseY + (int)(1.2f * sinf(ph * 0.6f + i)));
          if (g_masc[i].drop) {
            uint32_t cyc = (now + i * 300) % 900;
            lv_obj_set_y(g_masc[i].drop, 6 + (int)(cyc * 22 / 900));
            lv_obj_set_style_bg_color(g_masc[i].drop, lv_color_mix(lv_color_hex(C_BLUE), lv_color_hex(C_BG),
                                                                   (uint8_t)(255 - cyc * 190 / 900)), 0);
          }
        }
      }
    }
    uint32_t bp = blinkClosed ? 150 : 3000;
    if (mascLive && now - blinkAt > bp) {            // sbatte le palpebre (solo chi e' ok)
      blinkAt = now; blinkClosed = !blinkClosed;
      for (int i = 0; i < g_mascN; i++) {
        if (g_masc[i].mood != 1) continue;
        for (int k = 0; k < 2; k++) {
          if (!g_masc[i].lid[k]) continue;
          if (blinkClosed) lv_obj_clear_flag(g_masc[i].lid[k], LV_OBJ_FLAG_HIDDEN);
          else             lv_obj_add_flag(g_masc[i].lid[k], LV_OBJ_FLAG_HIDDEN);
        }
      }
    }
    if (g_slideSec > 0 && g_ui.tv && !g_refreshing && !g_mo.scrim && !g_nt.scrim && !g_tmMenu && !g_wxWeek && !g_shade && !g_calView && g_screenMode < 2 &&
        now - g_lastTouchMs > 10000 && now - g_lastSlideMs > (uint32_t)g_slideSec * 1000) {
      g_lastSlideMs = now;
      int next = (g_curTile + 1) % NTILES;
      lv_tileview_set_tile_by_index(g_ui.tv, next, 0, LV_ANIM_ON);
    }

    // pausa a tempo scaduta: riprende da sola
    if (g_userPause && g_pauseUntil) {
      time_t tn = time(nullptr);
      if (tn > 1000000000L && (uint32_t)tn >= g_pauseUntil) pause_set(false, 0);
    }
    // torna alla home dopo N minuti senza tocchi (una volta per periodo di inattivita')
    static uint32_t homedFor = 0;
    if (g_clockIdx && g_ui.tv && g_curTile != 0 && !g_mo.scrim && !g_nt.scrim && !g_pauseMenu && !g_tmMenu && !g_wxWeek && !g_shade && !g_calView && g_screenMode < 2 &&
        homedFor != g_lastTouchMs && now - g_lastTouchMs > CLOCK_MIN[g_clockIdx] * 60000UL) {
      homedFor = g_lastTouchMs;
      lv_tileview_set_tile_by_index(g_ui.tv, 0, 0, LV_ANIM_ON);
    }

    // avviso di Claude rimandato: appena finisce il focus e non c'e' altro a schermo
    if (g_ccDeferred && g_tmMode != TM_FOCUS && !g_ntPend && !g_nt.scrim) {
      g_ccDeferred = false;
      g_ntPend = NT_CLAUDE; g_ntT0 = 0;
    }
    // pannello a tendina (chiesto dal gesto nel driver del touch)
    if (g_shadeReq) {
      int r = g_shadeReq; g_shadeReq = 0;
      if (r == 2) shade_close();
      else if (!g_nt.scrim && !g_mo.scrim && !g_pauseMenu && !g_tmMenu && !g_wxWeek && g_screenMode < 2) shade_open(true);
    }
    // Momenti di soglia: mostra quello in sospeso e anima l'overlay attivo
    if (g_pendWin >= 0 && !g_mo.scrim && !g_refreshing && g_screenMode < 2) {
      show_moment(g_pendWin, g_pendThr);
      AlertRec ar = {};
      ar.at = (uint32_t)time(nullptr); ar.moment = true;
      ar.win = g_pendWin; ar.thr = g_pendThr; ar.peak = (uint8_t)g_pendPeak;
      al_push(ar);
      char t[64], m[64];
      const char *wn = g_pendWin ? TRS("7 giorni", "7-day") : TRS("5 ore", "5-hour");
      if (g_pendThr) {
        snprintf(t, sizeof(t), TRS("finestra %s al %d%%", "%s window at %d%%"), wn, g_pendThr);
        strlcpy(m, g_pendThr >= 100 ? TRS("limite raggiunto: attendi il reset", "limit reached: wait for the reset")
                                    : TRS("controlla il ritmo di utilizzo", "keep an eye on your usage pace"), sizeof(m));
      } else {
        snprintf(t, sizeof(t), TRS("finestra %s di nuovo disponibile", "%s window available again"), wn);
        strlcpy(m, TRS("si riparte", "back to work"), sizeof(m));
      }
      pc_notify(g_pendThr ? "thr" : "reset", t, m);
      g_pendWin = -1;
    }
    if (g_mo.scrim) moment_tick();
    // Avvisi di Claude Code e del timer: uno nuovo riaccende lo schermo. Di notte (schermo spento o
    // orologio) quelli di Claude Code non compaiono; il timer invece si', l'hai chiesto tu.
    if (g_ntPend == NT_CLAUDE && g_screenMode >= 2 && !g_ntT0) g_ntPend = NT_NONE;
    if (g_ntPend && !g_mo.scrim && !g_refreshing) {
      int k = g_ntPend;
      g_ntPend = NT_NONE;
      if (!g_ntT0) g_lastTouchMs = millis();
      if (k == NT_CLAUDE) cc_show(); else if (k == NT_CAL) cal_show(); else if (k == NT_BRK) brk_show(); else if (k == NT_CD) cd_show(); else if (k == NT_WK) wk_show(); else tm_show();
    }
    if (g_nt.scrim) notice_tick();
  }

  delay(5);
}
