lucamar90/ritmo-code/firmware/ritmo_code/api.cpp

#include "api.h"
#include "config.h"
#include "certs.h"
#include <Arduino.h>
#include <WiFiClientSecure.h>
#include "yield_client.h"
#include <HTTPClient.h>
#include <esp_heap_caps.h>

#define H5U "anthropic-ratelimit-unified-5h-utilization"
#define H5R "anthropic-ratelimit-unified-5h-reset"
#define H5S "anthropic-ratelimit-unified-5h-status"
#define D7U "anthropic-ratelimit-unified-7d-utilization"
#define D7R "anthropic-ratelimit-unified-7d-reset"
#define D7S "anthropic-ratelimit-unified-7d-status"
#define UST "anthropic-ratelimit-unified-status"
#define URS "anthropic-ratelimit-unified-reset"
#define URC "anthropic-ratelimit-unified-representative-claim"
#define UFB "anthropic-ratelimit-unified-fallback-percentage"
#define UOS "anthropic-ratelimit-unified-overage-status"
#define UOR "anthropic-ratelimit-unified-overage-disabled-reason"

static const char* RL_HEADERS[] = {
    H5U, H5R, H5S, D7U, D7R, D7S, UST, URS, URC, UFB, UOS, UOR
};
static const int RL_HEADER_COUNT = 12;

bool fetchUsage(const char* token, UsageData& out) {
    YieldSecureClient client;
    client.setCACert(CA_BUNDLE);

    HTTPClient https;
    if (!https.begin(client, MESSAGES_ENDPOINT)) {
        strlcpy(out.error, "https_init", sizeof(out.error));
        out.ok = false;
        return false;
    }

    https.addHeader("Authorization", String("Bearer ") + token);
    https.addHeader("anthropic-version", ANTHROPIC_VERSION);
    https.addHeader("anthropic-beta", "oauth-2025-04-20");
    https.addHeader("content-type", "application/json");
    https.addHeader("User-Agent", CLAUDE_CODE_UA);
    https.setTimeout(API_TIMEOUT_MS);
    https.collectHeaders(RL_HEADERS, RL_HEADER_COUNT);

    String body = "{\"model\":\"" PROBE_MODEL "\","
                  "\"max_tokens\":1,"
                  "\"system\":\"" CLAUDE_CODE_SYSTEM "\","
                  "\"messages\":[{\"role\":\"user\",\"content\":\".\"}]}";

    Serial.printf("[API] POST %s\n", MESSAGES_ENDPOINT);
    int code = https.POST(body);
    Serial.printf("[API] HTTP %d\n", code);

    if (code <= 0) {
        // causa vera della connessione mancata (TLS, memoria, socket): "http_-1" da solo non basta
        char le[48] = "";
        client.lastError(le, sizeof(le));
        snprintf(out.error, sizeof(out.error), "http_%d %s", code, le);
        Serial.printf("[API] errore: %s (RAM interna %u KB, blocco max %u KB)\n", out.error,
                      (unsigned)(heap_caps_get_free_size(MALLOC_CAP_INTERNAL) / 1024),
                      (unsigned)(heap_caps_get_largest_free_block(MALLOC_CAP_INTERNAL) / 1024));
        out.ok = false;
        https.end();
        return false;
    }

    String h5u = https.header(H5U);
    String d7u = https.header(D7U);

    if (h5u.length() == 0 && d7u.length() == 0) {
        if (code == 401) strlcpy(out.error, "auth_failed", sizeof(out.error));
        else snprintf(out.error, sizeof(out.error), "no_usage_h_%d", code);
        out.ok = false;
        https.end();
        return false;
    }

    out.h5 = h5u.toFloat() * 100.0f;
    out.d7 = d7u.toFloat() * 100.0f;
    out.h5ResetEpoch = (uint32_t)https.header(H5R).toInt();
    out.d7ResetEpoch = (uint32_t)https.header(D7R).toInt();
    out.unifiedResetEpoch = (uint32_t)https.header(URS).toInt();
    out.fallbackPct = https.header(UFB).toFloat() * 100.0f;

    strlcpy(out.statusOverall, https.header(UST).c_str(), sizeof(out.statusOverall));
    strlcpy(out.status5h,      https.header(H5S).c_str(), sizeof(out.status5h));
    strlcpy(out.status7d,      https.header(D7S).c_str(), sizeof(out.status7d));
    strlcpy(out.repClaim,      https.header(URC).c_str(), sizeof(out.repClaim));
    strlcpy(out.overageStatus, https.header(UOS).c_str(), sizeof(out.overageStatus));
    strlcpy(out.overageReason, https.header(UOR).c_str(), sizeof(out.overageReason));

    Serial.printf("[API] 5h:%.0f%% (%s)  7d:%.0f%% (%s)  claim:%s  overall:%s\n",
                  out.h5, out.status5h, out.d7, out.status7d, out.repClaim, out.statusOverall);

    https.end();
    out.ok = true;
    return true;
}

bool probeModel(const char* token, const char* modelId, ProbeResult& out) {
    YieldSecureClient client;
    client.setCACert(CA_BUNDLE);

    HTTPClient https;
    if (!https.begin(client, MESSAGES_ENDPOINT)) { out.code = -1; out.ms = 0; return false; }

    https.addHeader("Authorization", String("Bearer ") + token);
    https.addHeader("anthropic-version", ANTHROPIC_VERSION);
    https.addHeader("anthropic-beta", "oauth-2025-04-20");
    https.addHeader("content-type", "application/json");
    https.addHeader("User-Agent", CLAUDE_CODE_UA);
    https.setTimeout(API_TIMEOUT_MS);

    String body = String("{\"model\":\"") + modelId + "\","
                  "\"max_tokens\":1,"
                  "\"system\":\"" CLAUDE_CODE_SYSTEM "\","
                  "\"messages\":[{\"role\":\"user\",\"content\":\".\"}]}";

    uint32_t t0 = millis();
    int code = https.POST(body);
    uint32_t dt = millis() - t0;
    // fuori dal 200 conserva error.message: un 400 "versione troppo vecchia" o
    // "modello non supportato" dice molto piu' del solo codice
    out.msg[0] = 0;
    if (code < 0) client.lastError(out.msg, sizeof(out.msg));   // connessione mancata: errore TLS/rete
    if (code > 0 && code != 200) {
        String resp = https.getString();
        int a = resp.indexOf("\"message\":\"");
        if (a >= 0) {
            a += 11;
            int b = resp.indexOf('"', a);
            if (b < 0) b = resp.length();
            strlcpy(out.msg, resp.substring(a, b).c_str(), sizeof(out.msg));
        }
    }
    https.end();

    out.code = code;
    out.ms = (dt > 65000) ? 65000 : (uint16_t)dt;
    Serial.printf("[PROBE] %s -> HTTP %d (%ums) %s\n", modelId, code, (unsigned)dt, out.msg);
    return code == 200;
}
