lucamar90/ritmo-code/firmware/ritmo_code/status.cpp

#include "status.h"
#include "config.h"
#include "certs.h"
#include <Arduino.h>
#include <WiFiClientSecure.h>
#include "yield_client.h"
#include <HTTPClient.h>

bool fetchModelStatus(ModelStatus& out) {
    YieldSecureClient client;
    client.setCACert(CA_BUNDLE);

    HTTPClient https;
    if (!https.begin(client, STATUS_ENDPOINT)) {
        Serial.println("[STATUS] https_init failed");
        return false;
    }

    https.addHeader("User-Agent", "ritmo-code/1.0");
    https.setTimeout(API_TIMEOUT_MS);
    https.setFollowRedirects(HTTPC_STRICT_FOLLOW_REDIRECTS);

    Serial.printf("[STATUS] GET %s\n", STATUS_ENDPOINT);
    int code = https.GET();
    Serial.printf("[STATUS] HTTP %d\n", code);

    if (code != 200) {
        https.end();
        return false;   // mantiene l'ultimo stato noto
    }

    int len = https.getSize();
    if (len > 131072) {
        Serial.printf("[STATUS] body too large (%d)\n", len);
        https.end();
        return false;
    }

    String body = https.getString();
    https.end();

    body.toLowerCase();
    out.haikuUp  = body.indexOf("haiku")  < 0;
    out.sonnetUp = body.indexOf("sonnet") < 0;
    out.opusUp   = body.indexOf("opus")   < 0;
    out.fableUp  = body.indexOf("fable")  < 0;
    out.ok = true;

    Serial.printf("[STATUS] haiku:%d sonnet:%d opus:%d fable:%d\n",
                  out.haikuUp, out.sonnetUp, out.opusUp, out.fableUp);
    return true;
}
