lucamar90/ritmo-code/firmware/ritmo_code/extras.cpp

#include "extras.h"
#include <WiFi.h>
#include <HTTPClient.h>
#include <WiFiClientSecure.h>
#include "yield_client.h"
#include <Update.h>
#include "certs.h"
#include "config.h"

// ---- mini parser JSON: basta per le risposte piccole e note di Open-Meteo e Ritmo Code PC Monitor ----
// cerca "key" a partire da `from` e restituisce la posizione subito dopo i due punti (-1 se manca)
static int jkey(const String& s, const char* key, int from = 0) {
  String k = String("\"") + key + "\"";
  int i = s.indexOf(k, from);
  if (i < 0) return -1;
  i = s.indexOf(':', i + k.length());
  return i < 0 ? -1 : i + 1;
}
static float jnum(const String& s, const char* key, int from = 0, float def = 0) {
  int i = jkey(s, key, from);
  return i < 0 ? def : s.substring(i).toFloat();
}
// n-esimo elemento di un array: numero
static float jarr(const String& s, const char* key, int n, int from = 0, float def = 0) {
  int i = jkey(s, key, from);
  if (i < 0) return def;
  i = s.indexOf('[', i);
  if (i < 0) return def;
  int end = s.indexOf(']', i);                      // oltre la fine dell'array: valore mancante
  i++;
  for (int k = 0; k < n; k++) {
    i = s.indexOf(',', i);
    if (i < 0 || i > end) return def;
    i++;
  }
  return i >= end ? def : s.substring(i).toFloat();
}
// n-esimo elemento di un array di stringhe ISO: "2026-09-17T07:03" -> "07:03"
static void jarrTime(const String& s, const char* key, int n, int from, char* out) {
  out[0] = 0;
  int i = jkey(s, key, from);
  if (i < 0) return;
  i = s.indexOf('[', i);
  int open = -1;
  for (int k = 0; k <= n && i >= 0; k++) {
    open = s.indexOf('"', i + 1);                   // apertura della stringa k
    if (open < 0) return;
    i = s.indexOf('"', open + 1);                   // chiusura
  }
  if (open < 0 || i < 0) return;
  int t = s.indexOf('T', open);
  if (t < 0 || t > i) return;
  strlcpy(out, s.substring(t + 1, t + 6).c_str(), 6);
}

bool fetchWeather(float lat, float lon, WeatherData& out) {
  out.ok = false;
  YieldSecureClient client;
  client.setCACert(CA_BUNDLE);           // open-meteo.com: catena Let's Encrypt -> ISRG Root X1
  HTTPClient http;
  char url[360];
  snprintf(url, sizeof(url),
           "https://api.open-meteo.com/v1/forecast?latitude=%.4f&longitude=%.4f"
           "&current=temperature_2m,weather_code,is_day&hourly=precipitation_probability"
           "&daily=temperature_2m_max,temperature_2m_min,sunrise,sunset,weather_code,precipitation_probability_max"
           "&timezone=auto&forecast_days=7&forecast_hours=12", lat, lon);
  if (!http.begin(client, url)) return false;
  http.setTimeout(8000);
  int code = http.GET();
  if (code != 200) { http.end(); Serial.printf("[METEO] HTTP %d\n", code); return false; }
  String s = http.getString();
  http.end();

  int cur = s.indexOf("\"current\":");
  int hourly = s.indexOf("\"hourly\":");
  int daily = s.indexOf("\"daily\":");
  if (cur < 0 || hourly < 0 || daily < 0) return false;

  out.temp  = jnum(s, "temperature_2m", cur);
  out.code  = (int)jnum(s, "weather_code", cur);
  out.isDay = jnum(s, "is_day", cur, 1) > 0.5f;

  // ora della prima voce oraria ("2026-09-17T13:00")
  char h0[6]; jarrTime(s, "time", 0, hourly, h0);
  out.rainHour0 = h0[0] ? atoi(h0) : 0;
  for (int i = 0; i < 12; i++) {
    float p = jarr(s, "precipitation_probability", i, hourly, 0);
    out.rain[i] = (uint8_t)(p < 0 ? 0 : (p > 100 ? 100 : p));
  }
  out.days = 0;
  for (int d = 0; d < 7; d++) {
    const float NONE = -999;
    float mx = jarr(s, "temperature_2m_max", d, daily, NONE);
    if (mx == NONE) break;
    out.dmax[d]  = mx;
    out.dmin[d]  = jarr(s, "temperature_2m_min", d, daily);
    out.dcode[d] = (int)jarr(s, "weather_code", d, daily);
    float p = jarr(s, "precipitation_probability_max", d, daily);
    out.drain[d] = (uint8_t)(p < 0 ? 0 : (p > 100 ? 100 : p));
    out.days = d + 1;
  }
  out.tmax  = out.dmax[0];
  out.tmin  = out.dmin[0];
  out.tmax2 = out.dmax[1];
  out.tmin2 = out.dmin[1];
  out.code2 = out.dcode[1];
  jarrTime(s, "sunrise", 0, daily, out.sunrise);
  jarrTime(s, "sunset", 0, daily, out.sunset);
  out.ok = true;
  Serial.printf("[METEO] %.1f C, codice %d, max %.0f min %.0f\n", out.temp, out.code, out.tmax, out.tmin);
  return true;
}

// valore stringa di "key" (senza escape: bastano nomi di hardware)
static void jstrv(const String& s, const char* key, char* out, size_t sz, int from = 0) {
  out[0] = 0;
  int i = jkey(s, key, from);
  if (i < 0) return;
  int a = s.indexOf('"', i), b = a < 0 ? -1 : s.indexOf('"', a + 1);
  if (a < 0 || b < 0) return;
  strlcpy(out, s.substring(a + 1, b).c_str(), sz);
}

bool fetchPcStats(const char* host, PcStats& out) {
  out.ok = false;
  if (!host || !host[0]) return false;
  YieldClient client;
  HTTPClient http;
  String url = String("http://") + host + "/data.json";
  if (!http.begin(client, url)) return false;
  http.setConnectTimeout(3000);
  http.setTimeout(3000);
  uint32_t t0 = millis();
  int code = http.GET();
  static int lastCode = 200;
  if (code != lastCode) {                                  // log solo ai cambi di stato
    Serial.printf("[PC] %s -> %d (%s) in %lu ms\n", url.c_str(), code, code > 0 ? "http" : http.errorToString(code).c_str(),
                  (unsigned long)(millis() - t0));
    lastCode = code;
  }
  if (code != 200) { http.end(); return false; }
  String s = http.getString();
  http.end();
  if (s.indexOf("\"cpu_load\"") < 0) return false;
  out.cpu     = jnum(s, "cpu_load");
  out.cpuTemp = jnum(s, "cpu_temp");
  out.ram     = jnum(s, "ram_load");
  out.gpu     = jnum(s, "gpu_load");
  out.gpuTemp = jnum(s, "gpu_temp");
  out.disk    = jnum(s, "disk_used_pct");
  out.cpuMhz  = jnum(s, "cpu_mhz");
  out.cpuPower = jnum(s, "cpu_power");
  out.ramUsedMb = jnum(s, "ram_used_mb");
  // dati estesi
  out.extended = s.indexOf("\"cpu_name\"") >= 0;
  jstrv(s, "cpu_name", out.cpuName, sizeof(out.cpuName));
  jstrv(s, "gpu_name", out.gpuName, sizeof(out.gpuName));
  out.ramTotalMb  = jnum(s, "ram_total_mb");
  out.gpuPower    = jnum(s, "gpu_power");
  out.vramUsedMb  = jnum(s, "vram_used_mb");
  out.vramTotalMb = jnum(s, "vram_total_mb");
  out.netDown     = jnum(s, "net_down_bps");
  out.netUp       = jnum(s, "net_up_bps");
  out.diskRead    = jnum(s, "disk_read_bps");
  out.diskWrite   = jnum(s, "disk_write_bps");
  out.uptime      = (uint32_t)jnum(s, "uptime_s");
  out.claude      = (int)jnum(s, "claude_sessions", 0, -1);
  out.diskN = 0;
  int arr = s.indexOf("\"disks\"");
  int end = arr < 0 ? -1 : s.indexOf(']', arr);
  for (int p = arr; p >= 0 && out.diskN < PC_MAX_DISKS; ) {
    p = s.indexOf("\"d\":", p + 1);
    if (p < 0 || p > end) break;
    PcDisk &d = out.disks[out.diskN++];
    char l[4]; jstrv(s, "d", l, sizeof(l), p - 1);
    d.letter = l[0];
    d.used = jnum(s, "used_pct", p);
    d.freeGb = jnum(s, "free_gb", p);
    d.totalGb = jnum(s, "total_gb", p);
  }
  out.fanN = 0;
  arr = s.indexOf("\"fans\"");
  end = arr < 0 ? -1 : s.indexOf(']', arr);
  for (int p = arr; p >= 0 && out.fanN < PC_MAX_FANS; ) {
    p = s.indexOf("\"name\":", p + 1);
    if (p < 0 || p > end) break;
    PcFan &f = out.fans[out.fanN++];
    jstrv(s, "name", f.name, sizeof(f.name), p - 1);
    f.rpm = (int)jnum(s, "rpm", p);
  }
  // dettagli CPU/GPU e sensori di scheda madre, RAM e dischi
  out.cpuCoreMax  = jnum(s, "cpu_core_max", 0, -1);
  out.cpuVolt     = jnum(s, "cpu_voltage");
  out.gpuHotspot  = jnum(s, "gpu_hotspot");
  out.gpuMemTemp  = jnum(s, "gpu_mem_temp");
  out.gpuClockMhz = jnum(s, "gpu_clock_mhz");
  out.gpuMemLoad  = jnum(s, "gpu_mem_load", 0, -1);
  out.boardN = 0;
  arr = s.indexOf("\"board_temps\"");
  end = arr < 0 ? -1 : s.indexOf(']', arr);
  for (int p = arr; p >= 0 && out.boardN < 6; ) {
    p = s.indexOf("\"name\":", p + 1);
    if (p < 0 || p > end) break;
    PcTemp &b = out.board[out.boardN++];
    jstrv(s, "name", b.name, sizeof(b.name), p - 1);
    b.value = jnum(s, "value", p);
  }
  out.ramTempN = 0;
  arr = s.indexOf("\"ram_temps\"");
  if (arr >= 0) {
    int a0 = s.indexOf('[', arr), a1 = s.indexOf(']', arr);
    for (int p = a0; p >= 0 && p < a1 && out.ramTempN < 4; p = s.indexOf(',', p + 1)) {
      if (p + 1 >= a1) break;
      out.ramTemps[out.ramTempN++] = s.substring(p + 1).toFloat();
    }
  }
  out.driveN = 0;
  arr = s.indexOf("\"storage\"");
  end = arr < 0 ? -1 : s.indexOf(']', arr);
  for (int p = arr; p >= 0 && out.driveN < 4; ) {
    p = s.indexOf("\"name\":", p + 1);
    if (p < 0 || p > end) break;
    PcDrive &d = out.drives[out.driveN++];
    jstrv(s, "name", d.name, sizeof(d.name), p - 1);
    int obj = s.indexOf('}', p);
    int lp = s.indexOf("\"life\":", p);
    d.temp = jnum(s, "temp", p);
    d.life = (lp < 0 || lp > obj || s.substring(lp + 7).startsWith("null")) ? -1 : jnum(s, "life", p);
  }
  // Claude Code (hook): l'id supera la precisione di un float, si legge come intero
  int ci = jkey(s, "cc_ev_id");
  out.ccId = ci < 0 ? 0 : s.substring(ci).toInt();
  jstrv(s, "cc_ev", out.ccEv, sizeof(out.ccEv));
  jstrv(s, "cc_ev_proj", out.ccProj, sizeof(out.ccProj));
  out.ccDur  = (int)jnum(s, "cc_ev_dur", 0, -1);
  out.ccAge  = (int)jnum(s, "cc_ev_age", 0, 9999);
  out.ccBusy = (int)jnum(s, "cc_busy");
  out.actMin = (int)jnum(s, "act_min", 0, -1);
  for (int i = 0; i < 4; i++) {
    char k[8]; snprintf(k, sizeof(k), "cc_pj%d", i);
    jstrv(s, k, out.ccPj[i], sizeof(out.ccPj[i]));
    snprintf(k, sizeof(k), "cc_pl%d", i);
    jstrv(s, k, out.ccPl[i], sizeof(out.ccPl[i]));
  }
  jstrv(s, "cc_pa", out.ccPa, sizeof(out.ccPa));
  out.ssN = (int)jnum(s, "ss_n", 0, 0);
  if (out.ssN < 0) out.ssN = 0;
  if (out.ssN > 6) out.ssN = 6;
  for (int i = 0; i < out.ssN; i++) {
    char k[10];
    snprintf(k, sizeof(k), "ss%d_k", i);  jstrv(s, k, out.ss[i].k, sizeof(out.ss[i].k));
    snprintf(k, sizeof(k), "ss%d_p", i);  jstrv(s, k, out.ss[i].p, sizeof(out.ss[i].p));
    snprintf(k, sizeof(k), "ss%d_ti", i); jstrv(s, k, out.ss[i].ti, sizeof(out.ss[i].ti));
    snprintf(k, sizeof(k), "ss%d_s", i);  out.ss[i].s = (int)jnum(s, k, 0, 0);
    snprintf(k, sizeof(k), "ss%d_a", i);  out.ss[i].a = (int)jnum(s, k, 0, 0);
  }
  jstrv(s, "ss_fk", out.ssFk, sizeof(out.ssFk));
  jstrv(s, "ss_fr", out.ssFr, sizeof(out.ssFr));
  out.ssFa = (int)jnum(s, "ss_fa", 0, 99);
  out.mediaSt = (int)jnum(s, "media_st", 0, 0);
  if (out.mediaSt) {
    jstrv(s, "media_t", out.mediaTitle, sizeof(out.mediaTitle));
    jstrv(s, "media_a", out.mediaArtist, sizeof(out.mediaArtist));
    jstrv(s, "media_app", out.mediaApp, sizeof(out.mediaApp));
    out.mediaPos = (int)jnum(s, "media_pos");
    out.mediaDur = (int)jnum(s, "media_dur");
    out.mediaCv  = (int)jnum(s, "media_cv");
    out.mediaCtl = (int)jnum(s, "media_ctl", 0, 7);
    int mi = jkey(s, "media_id");
    out.mediaId = mi < 0 ? 0 : (uint32_t)s.substring(mi).toInt();
  }
  // calendario: cal_n e, per ogni evento, cal<i>_t (titolo), cal<i>_s / cal<i>_e (epoch)
  out.calN = (int)jnum(s, "cal_n", 0, -1);
  if (out.calN > 3) out.calN = 3;
  for (int i = 0; i < out.calN; i++) {
    char k[12];
    snprintf(k, sizeof(k), "cal%d_t", i); jstrv(s, k, out.cal[i].title, sizeof(out.cal[i].title));
    snprintf(k, sizeof(k), "cal%d_s", i); int ks = jkey(s, k); out.cal[i].s = ks < 0 ? 0 : (uint32_t)s.substring(ks).toInt();
    snprintf(k, sizeof(k), "cal%d_e", i); int ke = jkey(s, k); out.cal[i].e = ke < 0 ? 0 : (uint32_t)s.substring(ke).toInt();
  }
  out.ok = true;
  return true;
}

static String urlenc(const char* s) {
  String o;
  static const char* H = "0123456789ABCDEF";
  for (; *s; s++) {
    uint8_t c = (uint8_t)*s;
    if (isalnum(c) || c == '-' || c == '_' || c == '.') o += (char)c;
    else { o += '%'; o += H[c >> 4]; o += H[c & 15]; }
  }
  return o;
}

bool postPcNotify(const char* host, const char* ev, const char* title, const char* msg) {
  if (!host || !host[0]) return false;
  YieldClient client;
  HTTPClient http;
  if (!http.begin(client, String("http://") + host + "/notify")) return false;
  http.setConnectTimeout(2000);
  http.setTimeout(2000);
  http.addHeader("Content-Type", "application/x-www-form-urlencoded");
  String body = "ev=" + urlenc(ev) + "&title=" + urlenc(title) + "&msg=" + urlenc(msg);
  int code = http.POST(body);
  http.end();
  Serial.printf("[PC] avviso %s -> %d\n", ev, code);
  return code >= 200 && code < 300;
}

// ---- Aggiornamento del firmware dalle release di GitHub ----
// Ultima release: tag ("v3.9.3") e indirizzo del file ritmo-code-3.9.3.bin.
// Niente API JSON (risposta lunga e a pezzi: getString() girava a vuoto e il watchdog riavviava):
// basta il reindirizzamento di github.com/<repo>/releases/latest -> .../releases/tag/<tag>.
bool fetchLatestRelease(char* tag, size_t tagSz, char* url, size_t urlSz) {
  tag[0] = 0; url[0] = 0;
  YieldSecureClient client;
  client.setCACert(CA_BUNDLE);           // github.com: USERTrust ECC
  HTTPClient http;
  if (!http.begin(client, "https://github.com/" GITHUB_REPO "/releases/latest")) return false;
  http.setTimeout(10000);
  http.setUserAgent("ritmo-code");
  http.setFollowRedirects(HTTPC_DISABLE_FOLLOW_REDIRECTS);
  const char* keys[] = {"Location"};
  http.collectHeaders(keys, 1);
  int code = http.GET();
  String loc = http.header("Location");
  http.end();                            // il corpo non serve
  int t = loc.indexOf("/releases/tag/");
  if ((code != 301 && code != 302) || t < 0) { Serial.printf("[OTA] release: HTTP %d %s\n", code, loc.c_str()); return false; }
  strlcpy(tag, loc.substring(t + 14).c_str(), tagSz);
  const char* ver = tag[0] == 'v' ? tag + 1 : tag;
  snprintf(url, urlSz, "https://github.com/" GITHUB_REPO "/releases/download/%s/ritmo-code-%s.bin", tag, ver);
  Serial.printf("[OTA] ultima release %s\n", tag);
  return true;
}

// Scarica il .bin (GitHub reindirizza su release-assets.githubusercontent.com) e lo scrive
// nella partizione di aggiornamento; progress(0..100) a ogni blocco. true = pronto al riavvio.
bool installFromUrl(const char* url, void (*progress)(int pct), String& err) {
  YieldSecureClient client;
  client.setCACert(CA_BUNDLE);
  HTTPClient http;
  if (!http.begin(client, url)) { err = "indirizzo non valido"; return false; }
  http.setFollowRedirects(HTTPC_FORCE_FOLLOW_REDIRECTS);
  http.setUserAgent("ritmo-code");
  http.setTimeout(15000);
  int code = http.GET();
  if (code != 200) { err = String("download: HTTP ") + code; http.end(); return false; }
  int len = http.getSize();
  if (len <= 0) { err = "dimensione sconosciuta"; http.end(); return false; }
  if (!Update.begin(len, U_FLASH)) { err = String("spazio: ") + Update.errorString(); http.end(); return false; }
  WiFiClient* st = http.getStreamPtr();
  static uint8_t buf[4096];
  int done = 0, lastPct = -1;
  uint32_t idle = millis();
  while (done < len) {
    size_t av = st->available();
    if (!av) {
      if (!http.connected() || millis() - idle > 15000) break;
      delay(2);
      continue;
    }
    int r = st->readBytes(buf, av > sizeof(buf) ? sizeof(buf) : av);
    if (r <= 0) continue;
    if (Update.write(buf, r) != (size_t)r) { err = String("scrittura: ") + Update.errorString(); Update.abort(); http.end(); return false; }
    done += r; idle = millis();
    vTaskDelay(1);                       // cede il core: niente watchdog durante il download
    int pct = (int)((int64_t)done * 100 / len);
    if (pct != lastPct) { lastPct = pct; if (progress) progress(pct); }
  }
  http.end();
  if (done < len) { err = "download interrotto"; Update.abort(); return false; }
  if (!Update.end(true)) { err = String("verifica: ") + Update.errorString(); return false; }
  Serial.printf("[OTA] installato %d byte da %s\n", done, url);
  return true;
}

// {"n":..,"ev":[[inizio,fine,tutto_il_giorno,"titolo"],...]} (titoli gia' senza virgolette dal PC Monitor)
// ---- Pagina media: comandi e copertina dal PC Monitor ----
bool postPcMedia(const char* host, const char* action, int sec) {
  if (!host || !host[0]) return false;
  YieldClient client;
  HTTPClient http;
  if (!http.begin(client, String("http://") + host + "/media")) return false;
  http.setConnectTimeout(2000);
  http.setTimeout(2000);
  http.addHeader("Content-Type", "application/x-www-form-urlencoded");
  int code = http.POST(String("a=") + action + "&s=" + sec);
  http.end();
  Serial.printf("[MEDIA] %s -> %d\n", action, code);
  return code >= 200 && code < 300;
}
// ---- Pagina sessioni: apri la sessione sul PC (in primo piano, e se richiesto la scheda di Warp) ----
bool postPcSession(const char* host, const char* key, bool findTab) {
  if (!host || !host[0] || !key || !key[0]) return false;
  YieldClient client;
  HTTPClient http;
  if (!http.begin(client, String("http://") + host + "/session")) return false;
  http.setConnectTimeout(2000);
  http.setTimeout(2000);
  http.addHeader("Content-Type", "application/x-www-form-urlencoded");
  int code = http.POST(String("k=") + key + "&tab=" + (findTab ? "1" : "0"));
  http.end();
  Serial.printf("[SESS] apri %s -> %d\n", key, code);
  return code >= 200 && code < 300;
}
bool fetchPcCover(const char* host, uint8_t* buf, size_t len, uint32_t* id) {
  if (!host || !host[0] || !buf) return false;
  YieldClient client;
  HTTPClient http;
  if (!http.begin(client, String("http://") + host + "/media/cover.bin")) return false;
  http.setConnectTimeout(2000);
  http.setTimeout(4000);
  const char* keys[] = {"X-Media-Id"};
  http.collectHeaders(keys, 1);
  int code = http.GET();
  if (code != 200 || http.getSize() != (int)len) {
    Serial.printf("[MEDIA] copertina -> %d (%d byte)\n", code, http.getSize());
    http.end();
    return false;
  }
  if (id) *id = (uint32_t)http.header("X-Media-Id").toInt();
  WiFiClient* st = http.getStreamPtr();
  size_t got = 0;
  uint32_t t0 = millis();
  while (got < len && millis() - t0 < 5000) {
    size_t a = st->available();
    if (a) {
      int r = st->readBytes(buf + got, a < len - got ? a : len - got);
      if (r > 0) got += r;
    } else {
      if (!http.connected()) break;
      vTaskDelay(1);                     // niente attese a vuoto: il watchdog del core 0
    }
  }
  http.end();
  return got == len;
}

int fetchCalRange(const char* host, CalItem* out, int max) {
  if (!host || !host[0]) return -1;
  YieldClient client;
  HTTPClient http;
  if (!http.begin(client, String("http://") + host + "/calendar.json")) return -1;
  http.setConnectTimeout(3000);
  http.setTimeout(5000);
  int code = http.GET();
  if (code != 200) { http.end(); Serial.printf("[CAL] calendar.json -> %d\n", code); return -1; }
  String s = http.getString();
  http.end();
  int p = s.indexOf("\"ev\"");
  if (p < 0) return -1;
  p = s.indexOf('[', p);
  int n = 0;
  while (p >= 0 && n < max) {
    int a = s.indexOf('[', p + 1);
    if (a < 0) break;
    int c1 = s.indexOf(',', a), c2 = c1 < 0 ? -1 : s.indexOf(',', c1 + 1), c3 = c2 < 0 ? -1 : s.indexOf(',', c2 + 1);
    int q1 = c3 < 0 ? -1 : s.indexOf('"', c3), q2 = q1 < 0 ? -1 : s.indexOf('"', q1 + 1);
    if (q2 < 0) break;
    CalItem &it = out[n++];
    it.s = (uint32_t)s.substring(a + 1, c1).toInt();
    it.e = (uint32_t)s.substring(c1 + 1, c2).toInt();
    it.allday = s.substring(c2 + 1, c3).toInt() ? 1 : 0;
    strlcpy(it.title, s.substring(q1 + 1, q2).c_str(), sizeof(it.title));
    p = s.indexOf(']', q2);
  }
  Serial.printf("[CAL] %d eventi del periodo dal PC\n", n);
  return n;
}
